flypie/SSEM-Baby/Docs/ctrlgate.pdf

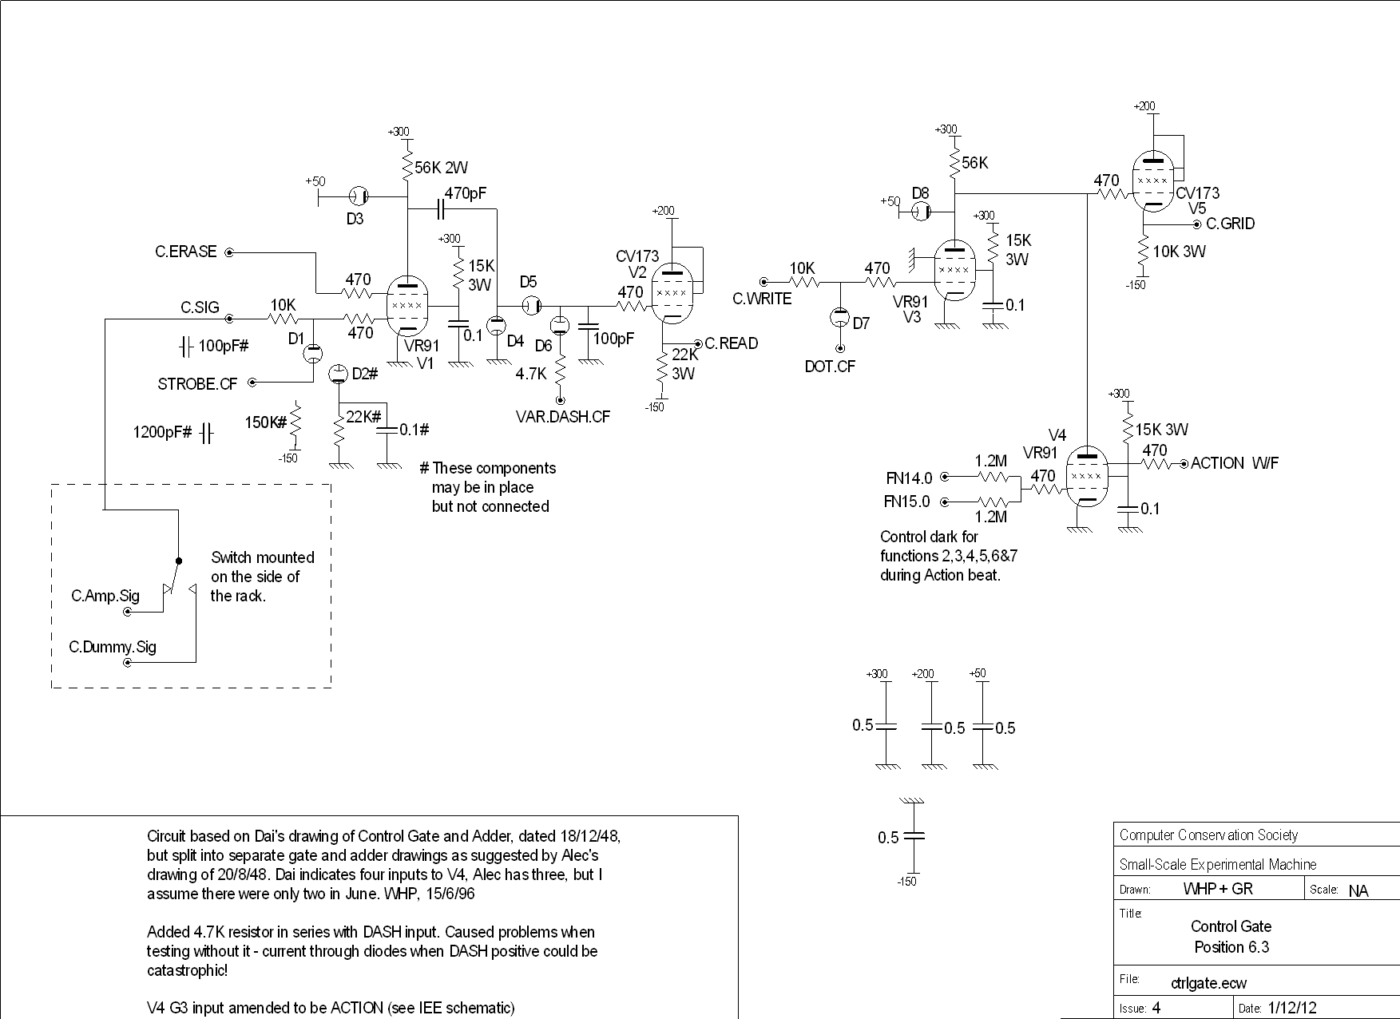
[picture p8: page 1]
