flypie/SSEM-Baby/Docs/transfer.pdf

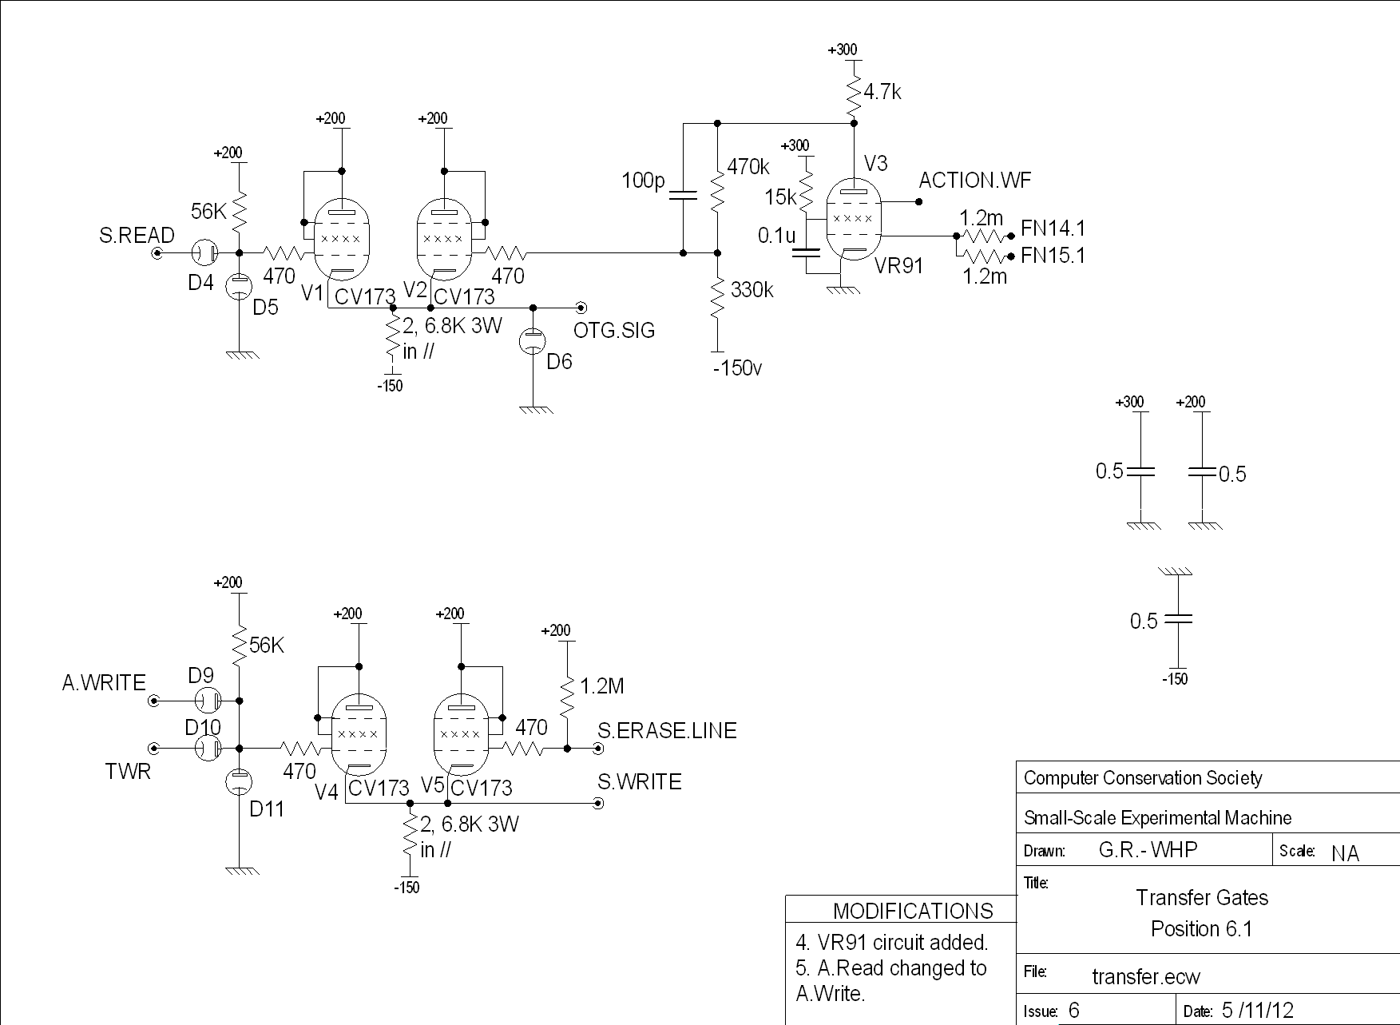
[picture p9: page 1]
