flypie/SSEM-Baby/Docs/crtamp3.pdf

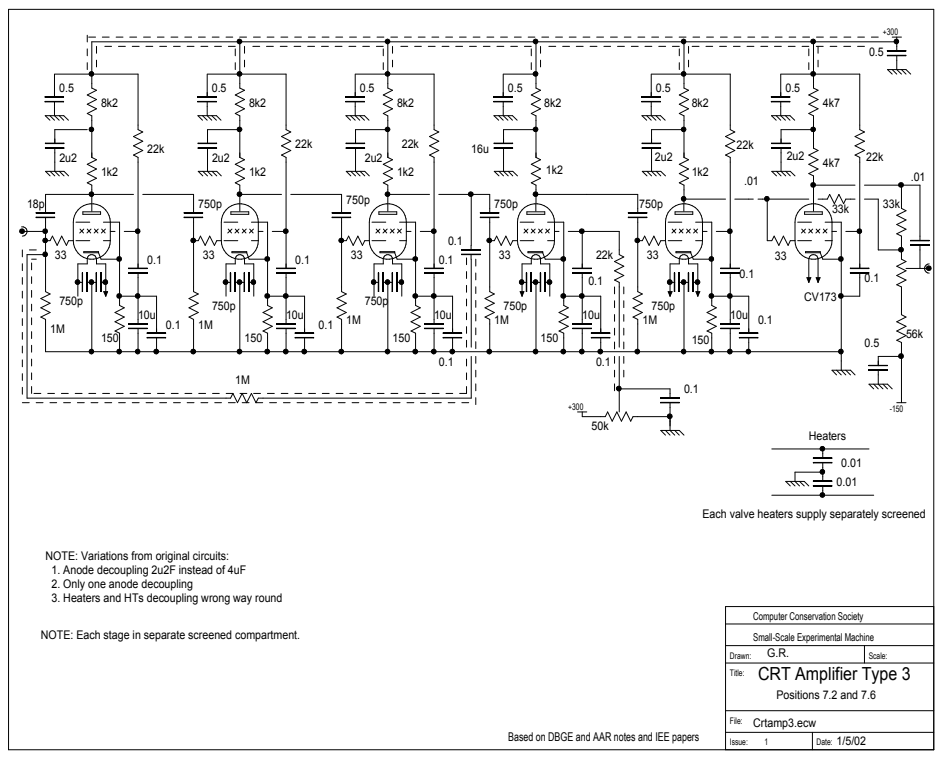
[picture p18: page 1]
Drawn:; Scale:; Title:; File:; Issue:; Date:; Heaters; Crtamp3.ecw; Positions 7.2 and 7.6

Each valve heaters supply separately screened

NOTE: Variations from original circuits:
1. Anode decoupling 2u2F instead of 4uF
2. Only one anode decoupling
3. Heaters and HTs decoupling wrong way round

Computer Conservation Society

NOTE: Each stage in separate screened compartment.

Small-Scale Experimental Machine
CRT Amplifier Type 3

1 Based on DBGE and AAR notes and IEE papers
