flypie/SSEM-Baby/Docs/crtamp4.pdf

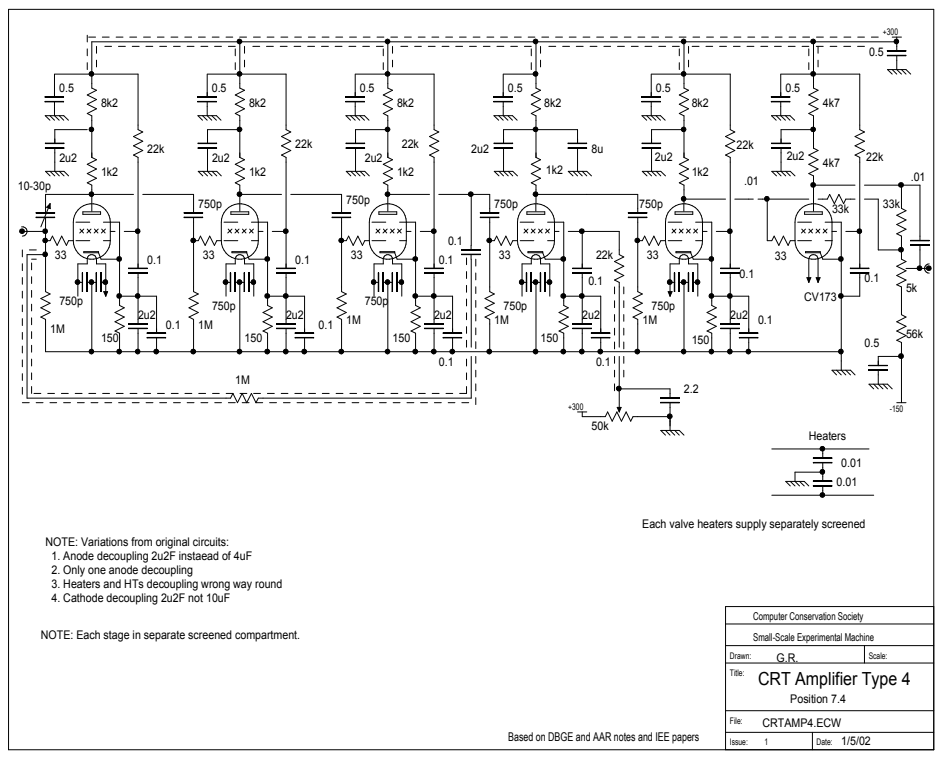
[picture p19: page 1]
Drawn:; Scale:; Title:; File:; Issue:; Date:; Heaters; Position 7.4; CRTAMP4.ECW

Each valve heaters supply separately screened

NOTE: Variations from original circuits:
1. Anode decoupling 2u2F instaead of 4uF
2. Only one anode decoupling
3. Heaters and HTs decoupling wrong way round
4. Cathode decoupling 2u2F not 10uF

Computer Conservation Society

NOTE: Each stage in separate screened compartment.

Small-Scale Experimental Machine
CRT Amplifier Type 4

1 Based on DBGE and AAR notes and IEE papers
