flypie/SSEM-Baby/Docs/crtcct3.pdf

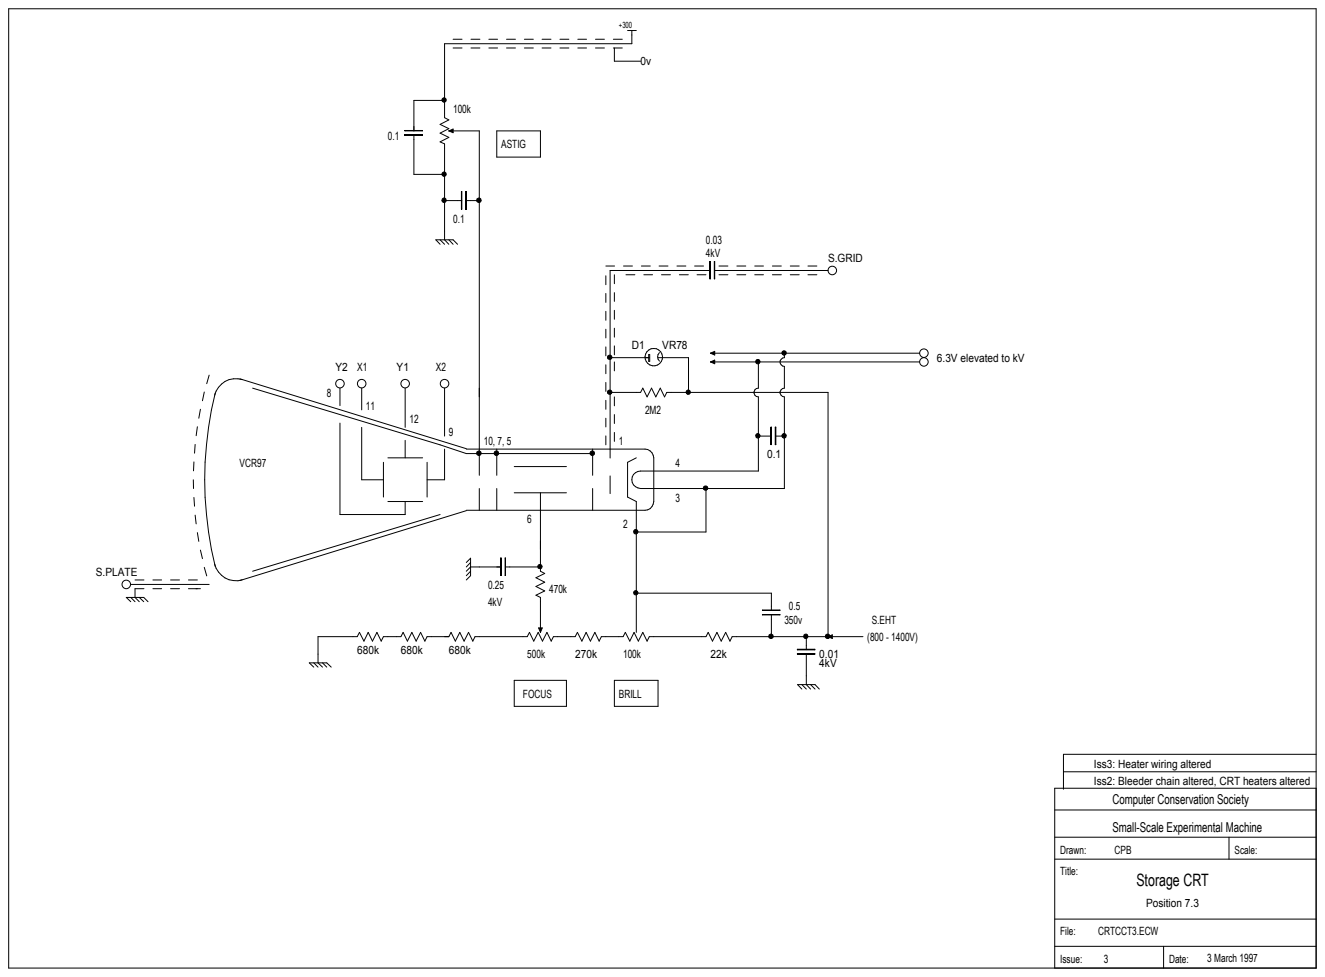
[picture p20: page 1]
Drawn:; Scale:; Title:; File:; Issue:; Date:; CPB; BRILL; FOCUS; VCR97; ASTIG; 3 March 1997; CRTCCT3.ECW; S.PLATE; S.GRID; Storage CRT; Position 7.3; S.EHT

6.3V elevated to kV

Iss3: Heater wiring altered
Iss2: Bleeder chain altered, CRT heaters altered
Computer Conservation Society

Small-Scale Experimental Machine
