flypie/SSEM-Baby/Docs/crtcct4.pdf

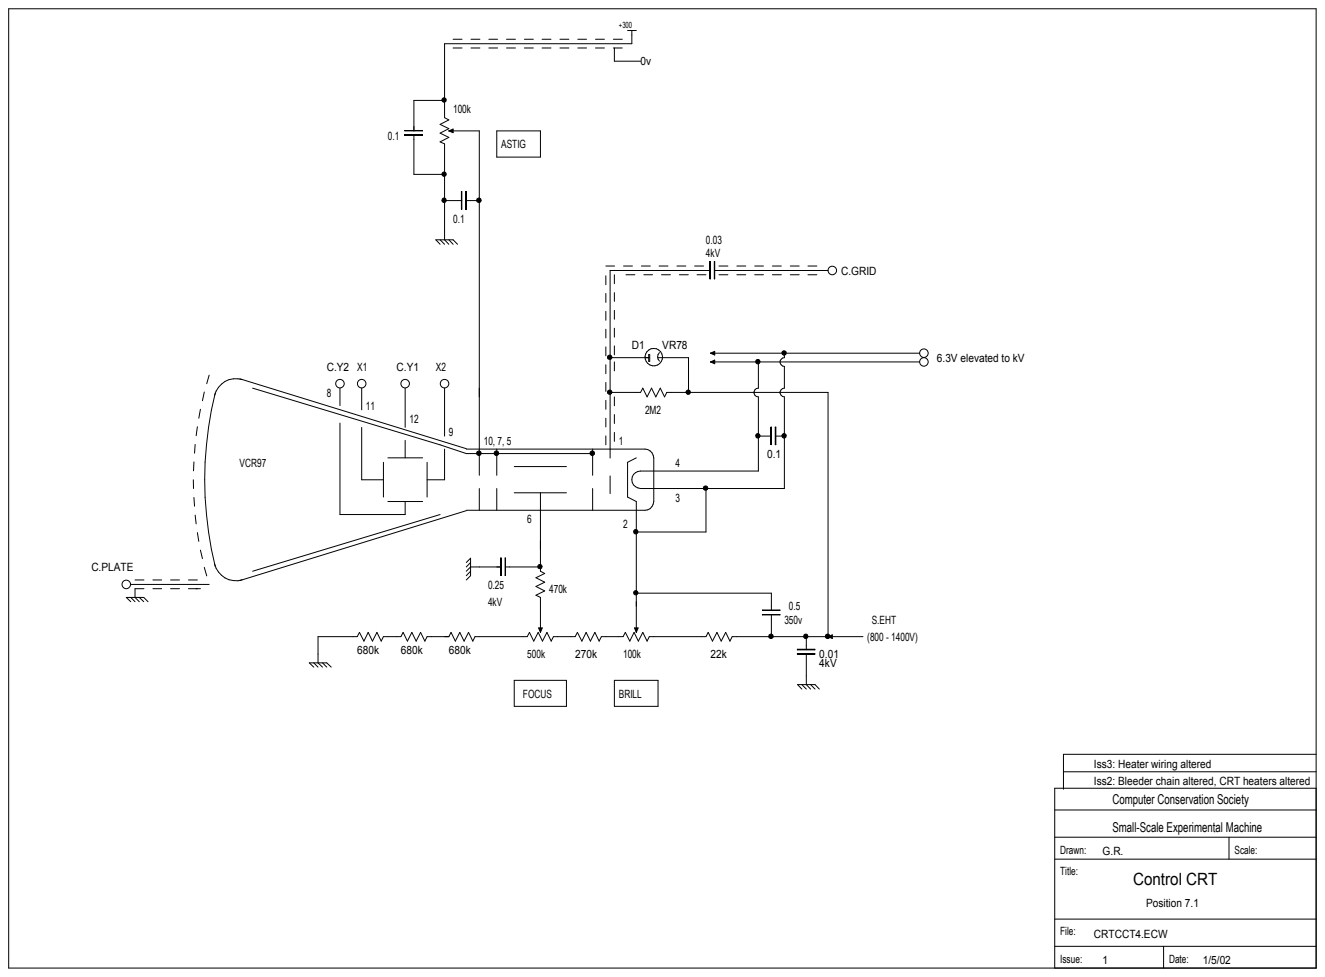
[picture p21: page 1]
Drawn:; Scale:; Title:; File:; Issue:; Date:; BRILL; FOCUS; VCR97; ASTIG; C.PLATE; C.GRID; Position 7.1; Control CRT; CRTCCT4.ECW; S.EHT

6.3V elevated to kV

Iss3: Heater wiring altered
Iss2: Bleeder chain altered, CRT heaters altered
Computer Conservation Society

Small-Scale Experimental Machine
