flypie/SSEM-Baby/Docs/crtcct5.pdf

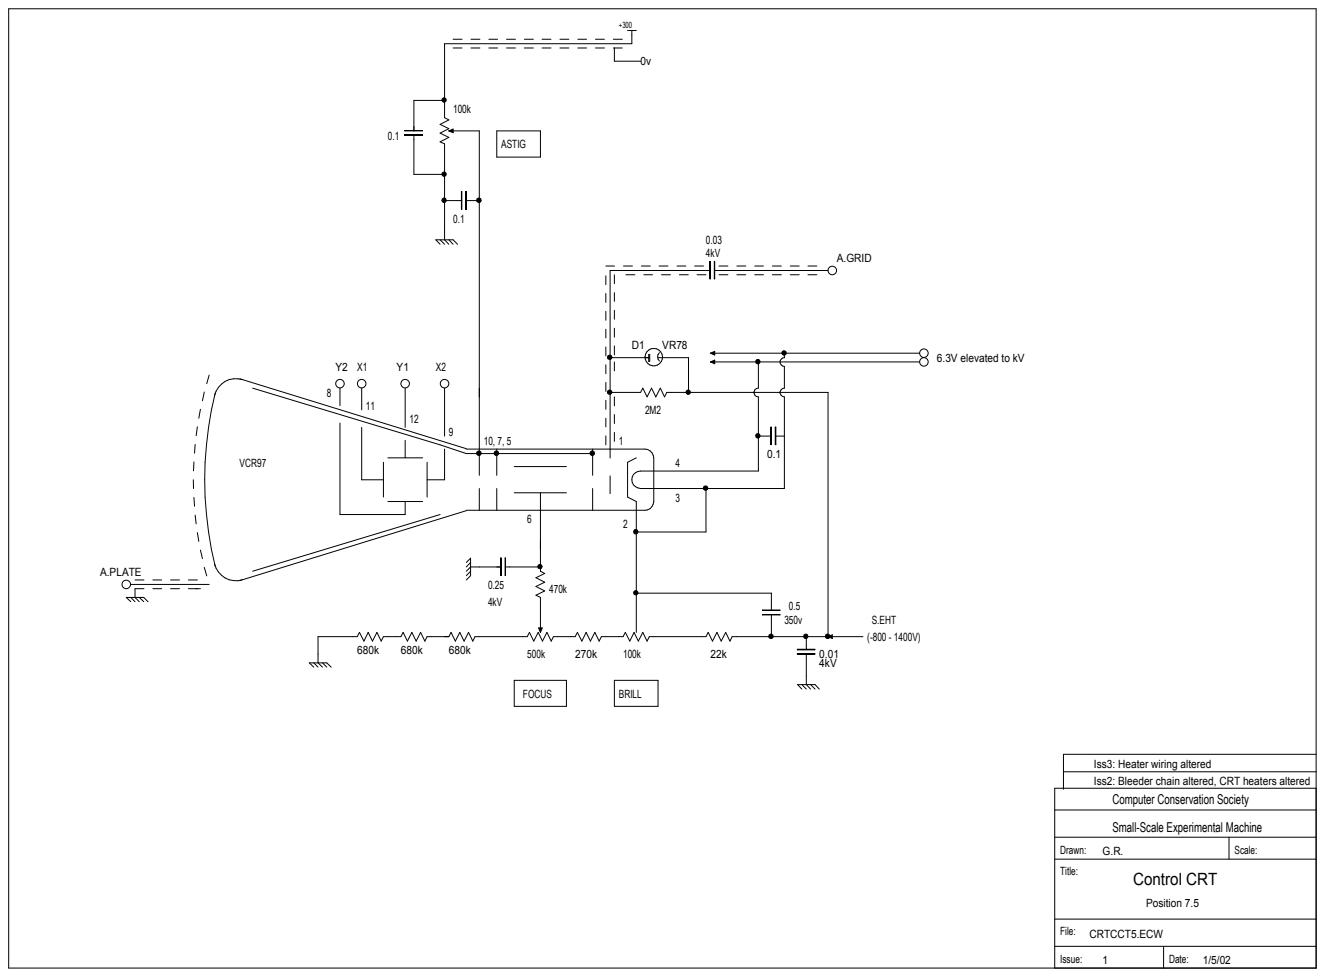
[picture p22: page 1]
Drawn:; Scale:; Title:; File:; Issue:; Date:; BRILL; FOCUS; VCR97; ASTIG; Control CRT; A.PLATE; A.GRID; Position 7.5; CRTCCT5.ECW; S.EHT

6.3V elevated to kV

Iss3: Heater wiring altered
Iss2: Bleeder chain altered, CRT heaters altered
Computer Conservation Society

Small-Scale Experimental Machine
