flypie/SSEM-Baby/Docs/crthtrtf.pdf

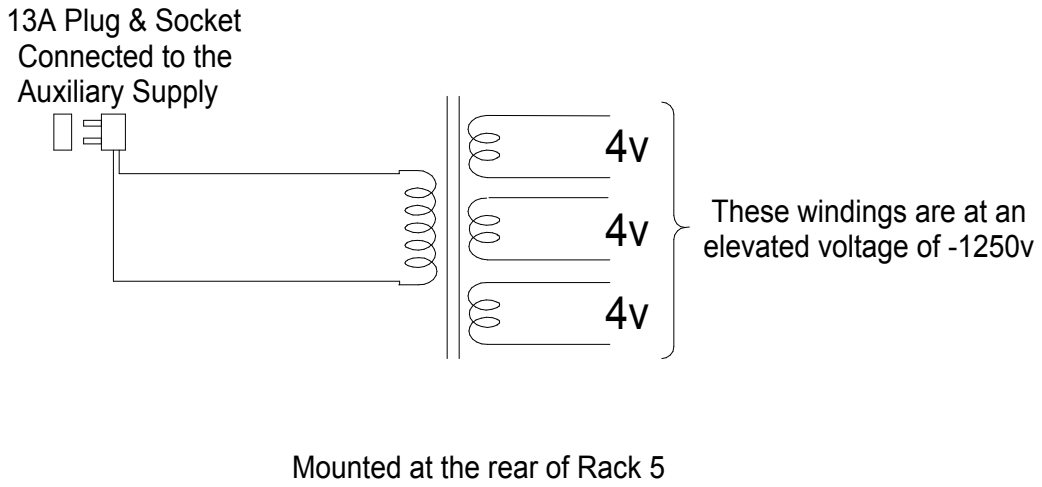
[picture p23: page 1]
Drawn:; Scale:; Title:; File:; Issue:; Date:; CRTHTRTF.ECW; Position 5.9

13A Plug & Socket
Connected to the
Auxiliary Supply

These windings are at an

elevated voltage of -1250v

Mounted at the rear of Rack 5

Computer Conservation Society

Small-Scale Experimental Machine

CRT Heater Transformer
