flypie/SSEM-Baby/Docs/crtpcif2.pdf

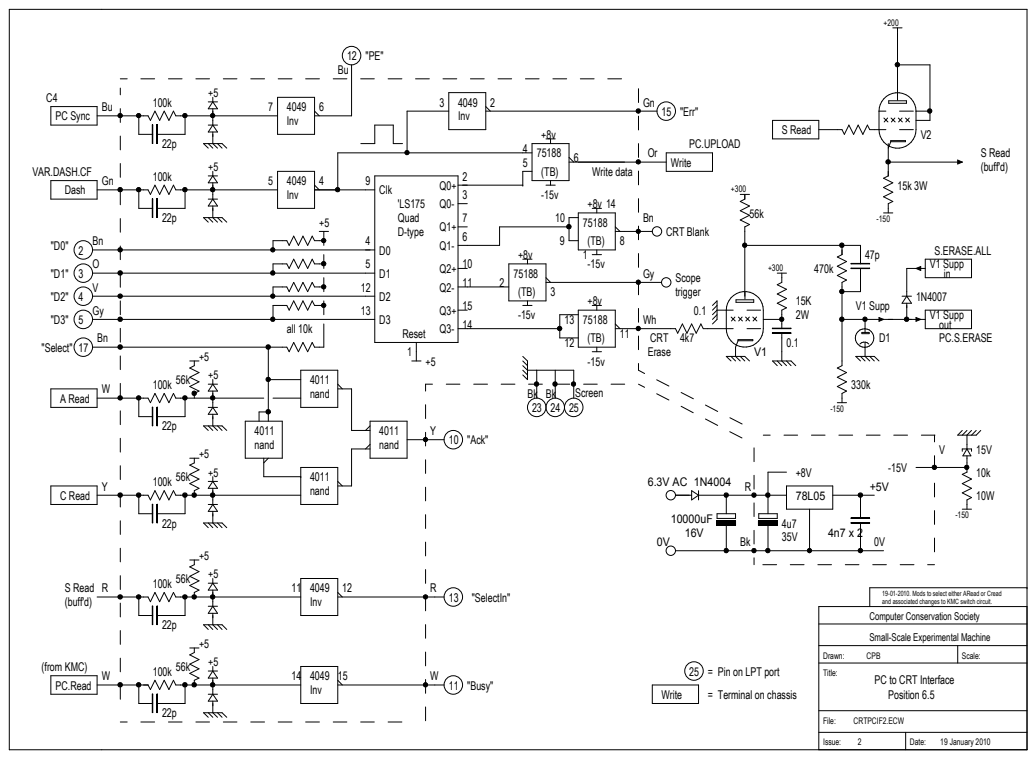
[picture p24: page 1]
Drawn:; Scale:; Title:; File:; Issue:; Date:; CPB; CRTPCIF2.ECW; 19 January 2010; S Read; S Read (buff'd); Clk; 'LS175 Quad D-type; Reset; 4049 Inv; CRT Blank; Scope trigger; Write; Write data; 15 "Err"; Inv; V1 Supp; out V1 Supp; V1 Supp in; CRT Erase; PC.UPLOAD; PC.S.ERASE; S.ERASE.ALL; Dash; PC Sync; VAR.DASH.CF; PC.Read; 11 "Busy"; Screen; C Read; 10 "Ack"; 4011 nand; A Read; (buff'd); "SelectIn"; "Select"; all 10k; (from KMC)

19-01-2010. Mods to select either ARead or Cread
and associated changes to KMC switch circuit.
Computer Conservation Society

Small-Scale Experimental Machine

= Pin on LPT port

PC to CRT Interface
Position 6.5

= Terminal on chassis
