flypie/SSEM-Baby/Docs/dchtrpu.pdf

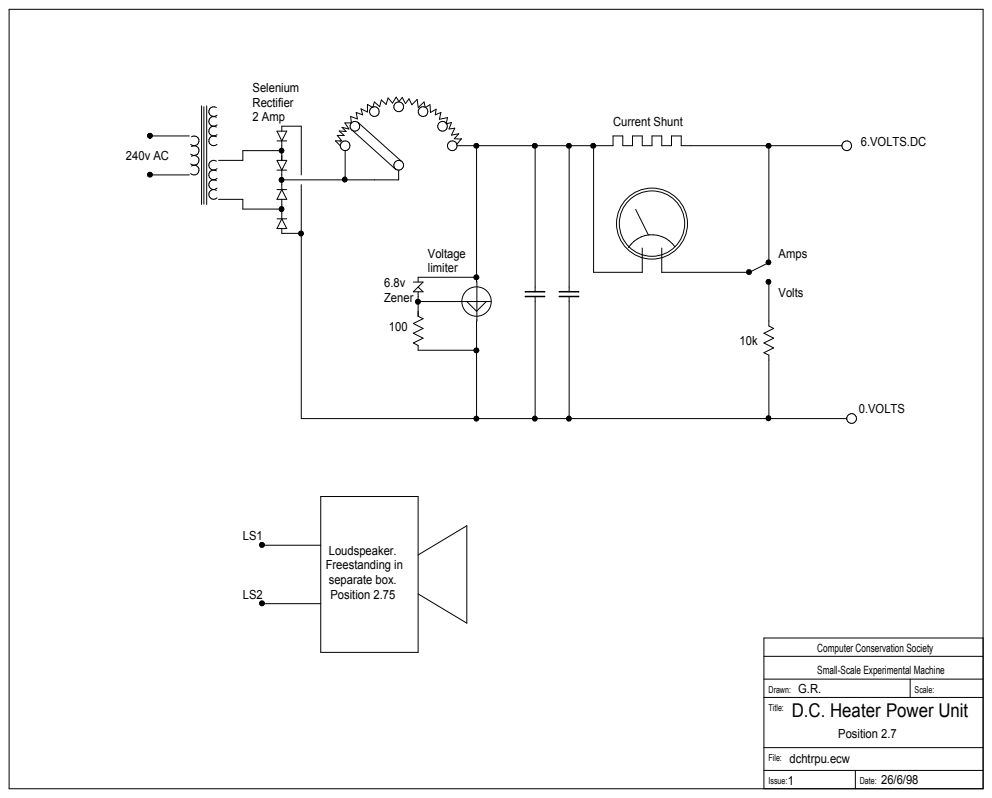
[picture p25: page 1]
Drawn:; Scale:; File:; Issue:; Date:; dchtrpu.ecw; Current Shunt; Selenium Rectifier 2 Amp; Voltage limiter; Amps; Volts; Position 2.7; 6.VOLTS.DC; 0.VOLTS; Loudspeaker. Freestanding in separate box. Position 2.75; 6.8v Zener

Computer Conservation Society

Small-Scale Experimental Machine
D.C. Heater Power Unit
Title:
