flypie/SSEM-Baby/Docs/keysw1.pdf

L 4 | L 3 | L 2 | L 1 | L 0

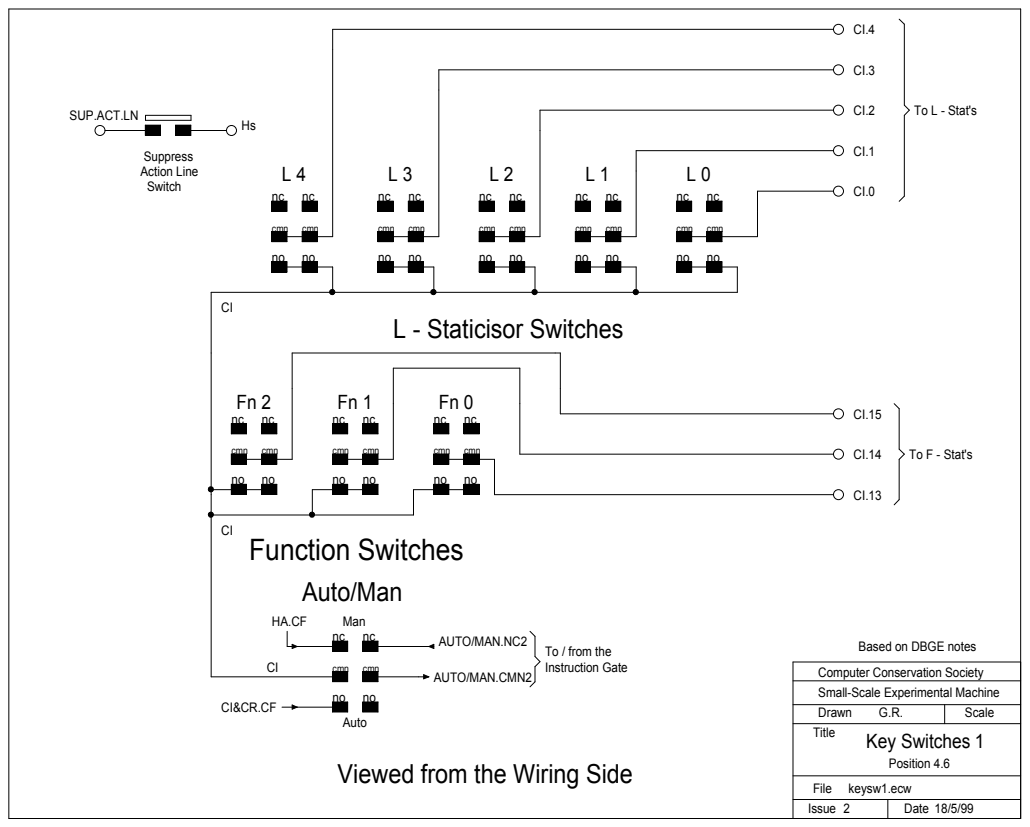
[picture p26: page 1]
Drawn; Scale; File; Issue; Date; keysw1.ecw; Auto/Man; Man; Auto; L - Staticisor Switches; Function Switches; AUTO/MAN.NC2; AUTO/MAN.CMN2; To L - Stat's; To F - Stat's; Position 4.6; Suppress Action Line Switch; cmn

SUP.ACT.LN

To / from the
Instruction Gate

Based on DBGE notes

Computer Conservation Society
Small-Scale Experimental Machine
Title
Key Switches 1

Viewed from the Wiring Side
