flypie/SSEM-Baby/Docs/keysw2.pdf

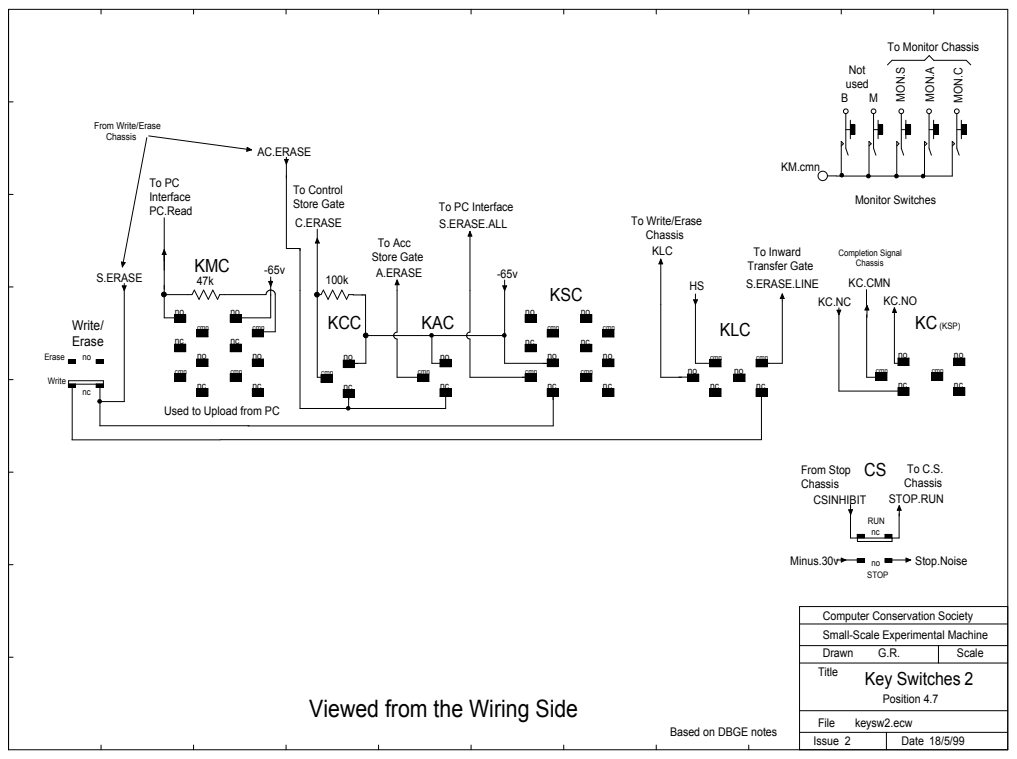
[picture p27: page 1]
Drawn; Scale; File; Issue; Date; keysw2.ecw; Write/ Erase; Write; Erase; S.ERASE; Position 4.7; From Stop Chassis; To C.S. Chassis; CSINHIBIT; STOP.RUN; RUN; Minus.30v; Stop.Noise; STOP; KCC; KAC; KSC; KLC; KC(KSP); C.ERASE; To Control Store Gate; A.ERASE; S.ERASE.ALL; To Acc Store Gate; S.ERASE.LINE; To Inward Transfer Gate; Completion Signal Chassis; KC.CMN; Monitor Switches; KM.cmn; Not used; MON.S; MON.A; MON.C; KMC; AC.ERASE; To PC Interface; PC.Read; cmn

To Monitor Chassis

From Write/Erase
Chassis

To Write/Erase
KLC

Used to Upload from PC

Computer Conservation Society
Small-Scale Experimental Machine
Title
Key Switches 2

Viewed from the Wiring Side

Based on DBGE notes
