flypie/SSEM-Baby/Docs/kvpsu1.pdf

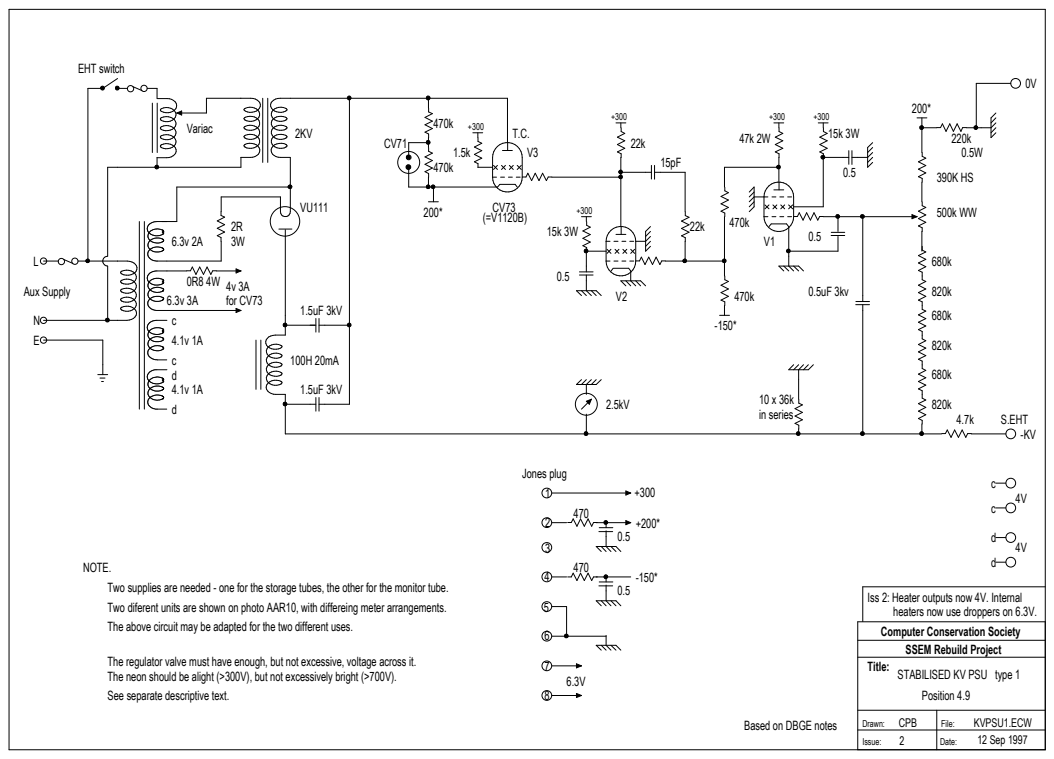
[picture p28: page 1]
Aux Supply; EHT switch; 2KV Variac; 10 x 36k in series; Jones plug; for CV73; S.EHT

NOTE.
Two supplies are needed - one for the storage tubes, the other for the monitor tube.
Two diferent units are shown on photo AAR10, with differeing meter arrangements.
The above circuit may be adapted for the two different uses.

Iss 2: Heater outputs now 4V. Internal
heaters now use droppers on 6.3V.
Computer Conservation Society
SSEM Rebuild Project

The regulator valve must have enough, but not excessive, voltage across it.
The neon should be alight (>300V), but not excessively bright (>700V).
See separate descriptive text.

Title:
STABILISED KV PSU type 1
Position 4.9

Based on DBGE notes

Drawn: CPB | KVPSU1.ECW File:

2 Issue: | 12 Sep 1997 Date:
