flypie/SSEM-Baby/Docs/kvpsu2.pdf

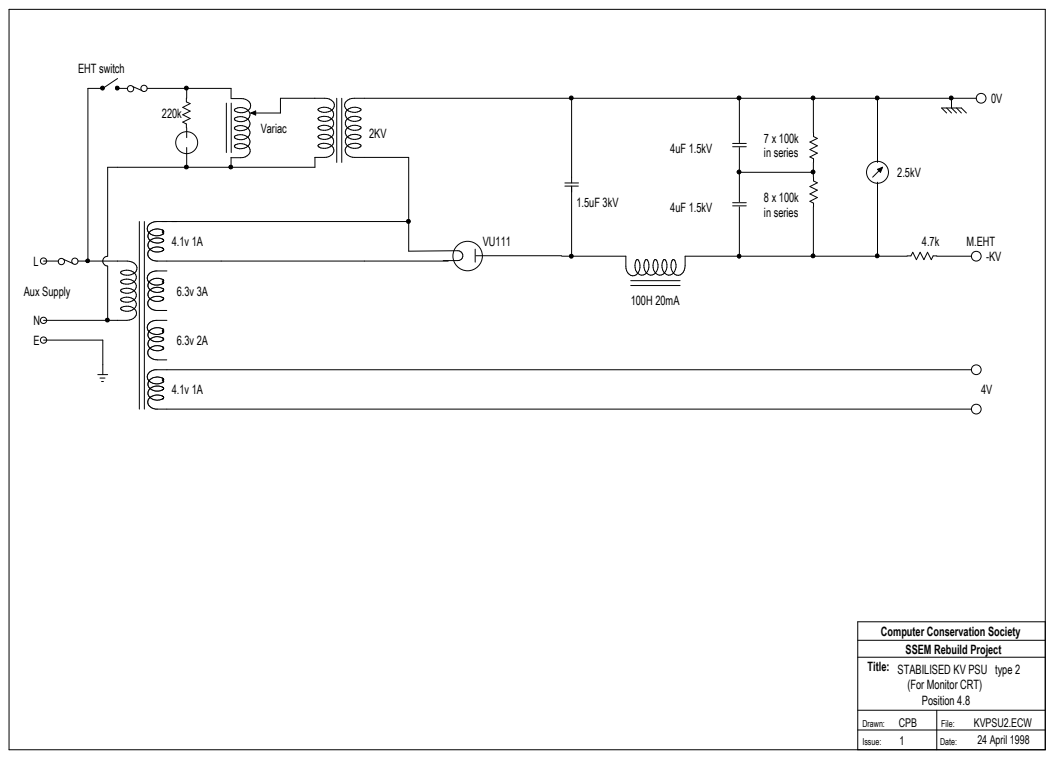
[picture p29: page 1]
Aux Supply; EHT switch; Title:; 2KV Variac; 7 x 100k in series; 8 x 100k in series; M.EHT

Computer Conservation Society
SSEM Rebuild Project
STABILISED KV PSU type 2
(For Monitor CRT)
Position 4.8

Drawn: CPB | KVPSU2.ECW File:

1 Issue: | 24 April 1998 Date:
