flypie/SSEM-Baby/Docs/monicct.pdf

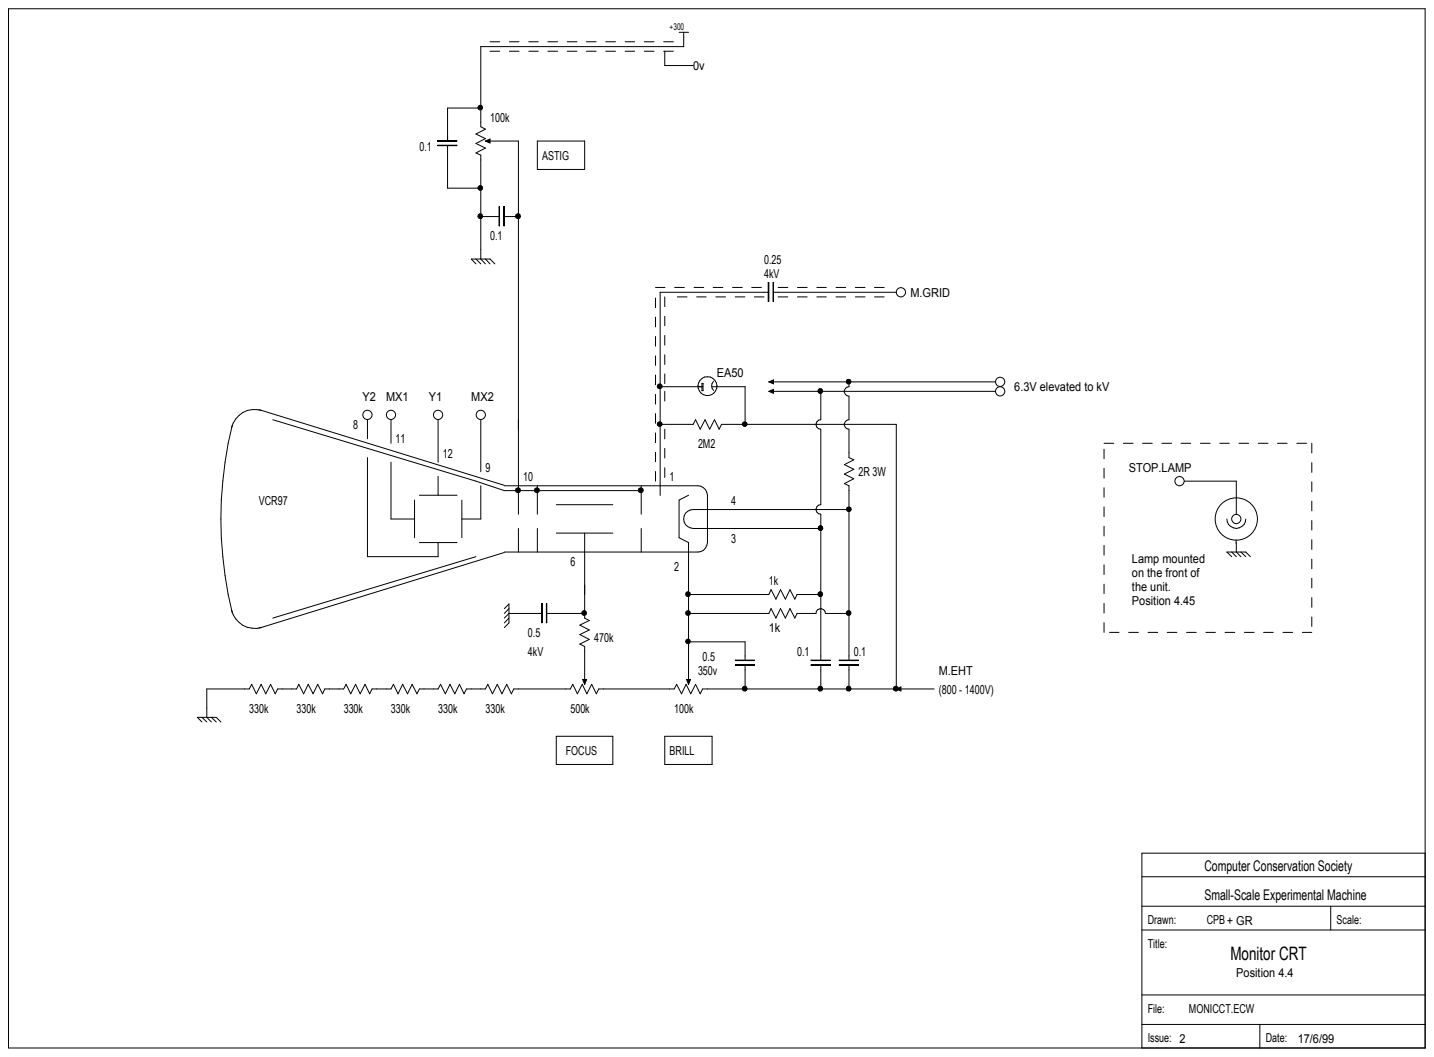
[picture p30: page 1]
Drawn:; Scale:; Title:; File:; Issue:; Date:; CPB; BRILL; FOCUS; VCR97; ASTIG; MONICCT.ECW; M.EHT; M.GRID; Monitor CRT; Position 4.4; STOP.LAMP

6.3V elevated to kV

Lamp mounted
on the front of
the unit.
Position 4.45

Computer Conservation Society

Small-Scale Experimental Machine
