flypie/SSEM-Baby/Docs/powrctl6b.pdf

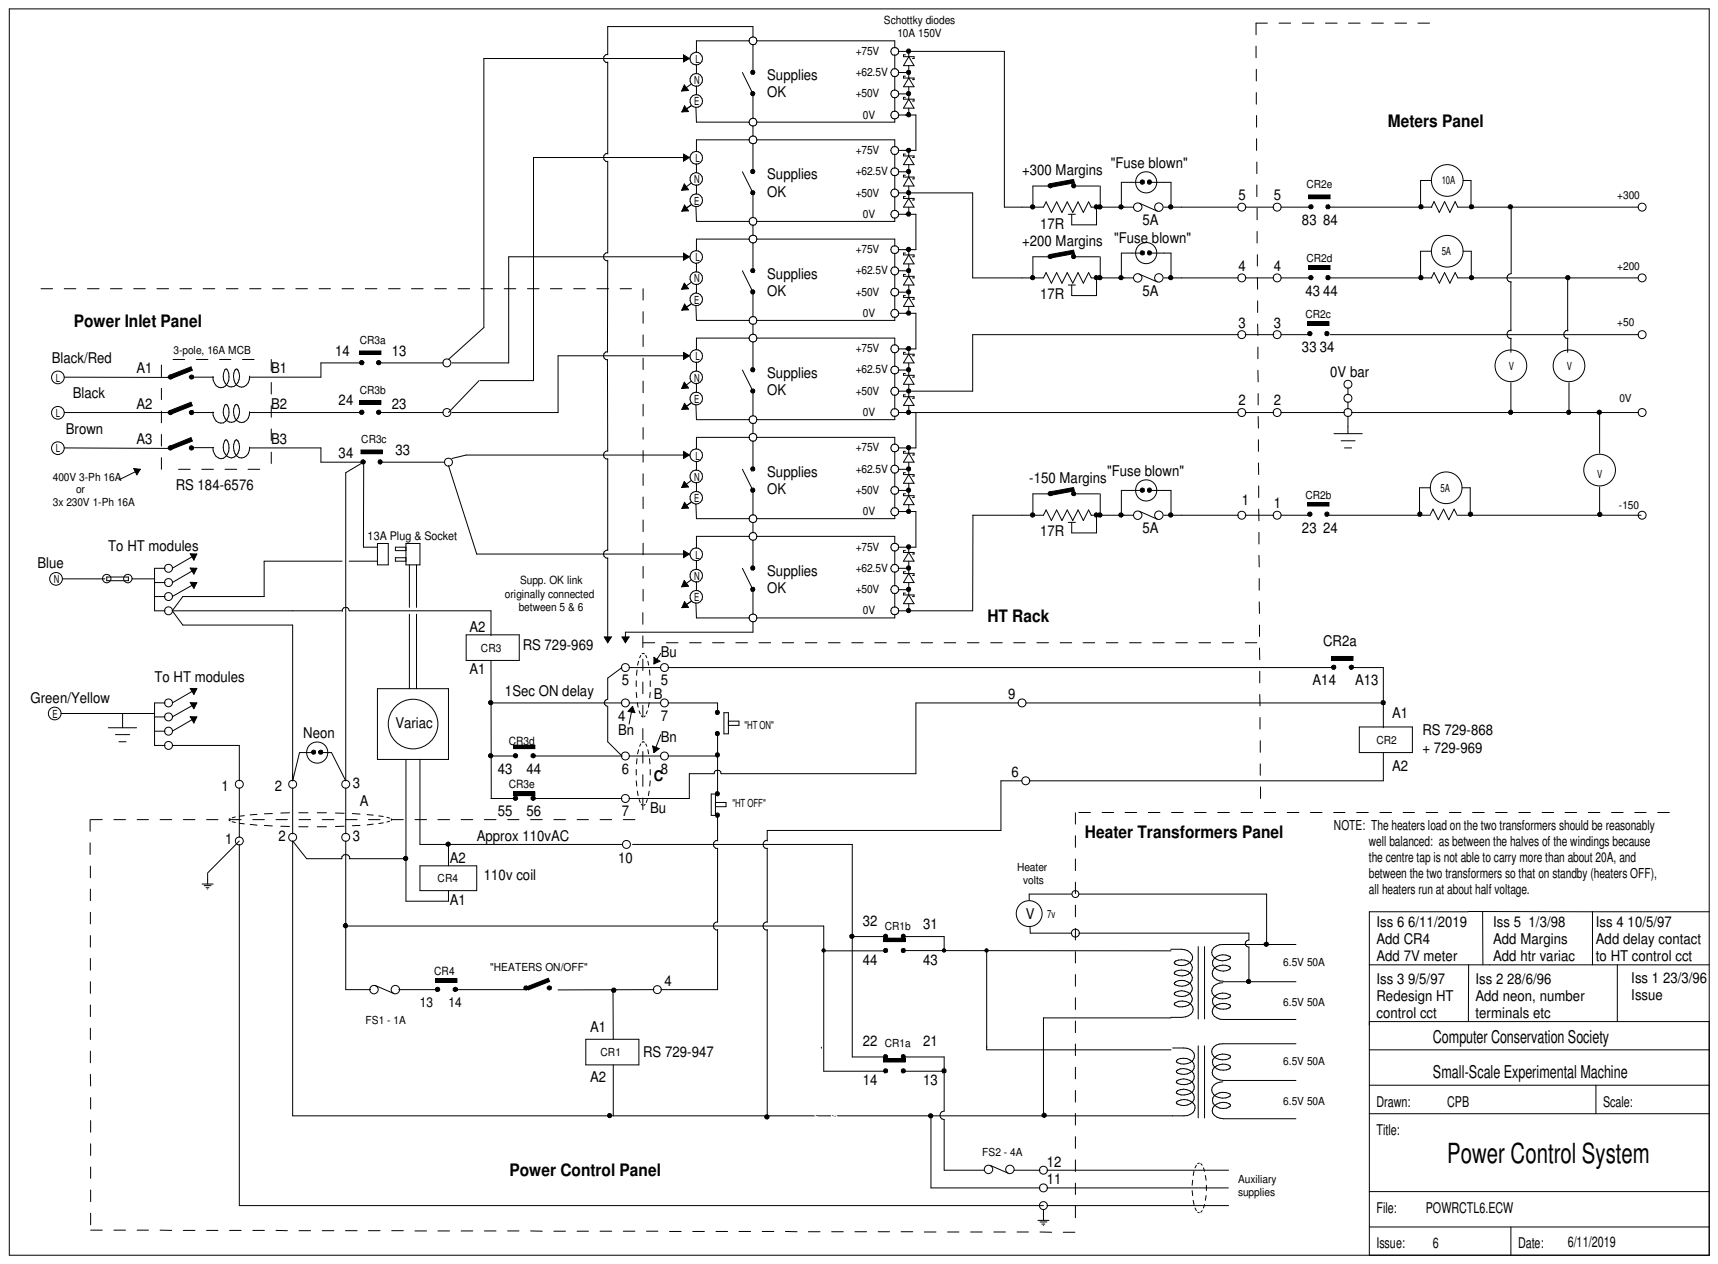
[picture p31: page 1]
Drawn:; Scale:; Title:; File:; Issue:; Date:; CPB; HT Rack; "HT OFF"; 1Sec ON delay; 13A Plug & Socket; Blue; Supplies OK; Green/Yellow; 3-pole, 16A MCB; Black/Red; Black; Brown; Schottky diodes 10A 150V; CR3d Neon; Auxiliary supplies; Heater volts; Variac; V 0V bar; "Fuse blown"; +300 Margins; +200 Margins; 110v coil; Approx 110vAC; POWRCTL6.ECW; Meters Panel

Power Inlet Panel

"Fuse blown" -150 Margins

To HT modules

Supp. OK link
originally connected
between 5 & 6

Heater Transformers Panel

NOTE: The heaters load on the two transformers should be reasonably
well balanced: as between the halves of the windings because
the centre tap is not able to carry more than about 20A, and
between the two transformers so that on standby (heaters OFF),
all heaters run at about half voltage.

Iss 6 6/11/2019 Add CR4 Add 7V meter | Iss 5 1/3/98 Add Margins Add htr variac | Iss 4 10/5/97 Add delay contact to HT control cct

"HEATERS ON/OFF"

Iss 3 9/5/97 Redesign HT control cct | Iss 2 28/6/96 Add neon, number terminals etc | Iss 1 23/3/96 Issue

Computer Conservation Society

Small-Scale Experimental Machine

Power Control System

Power Control Panel
