flypie/SSEM-Baby/Docs/prepulse.pdf

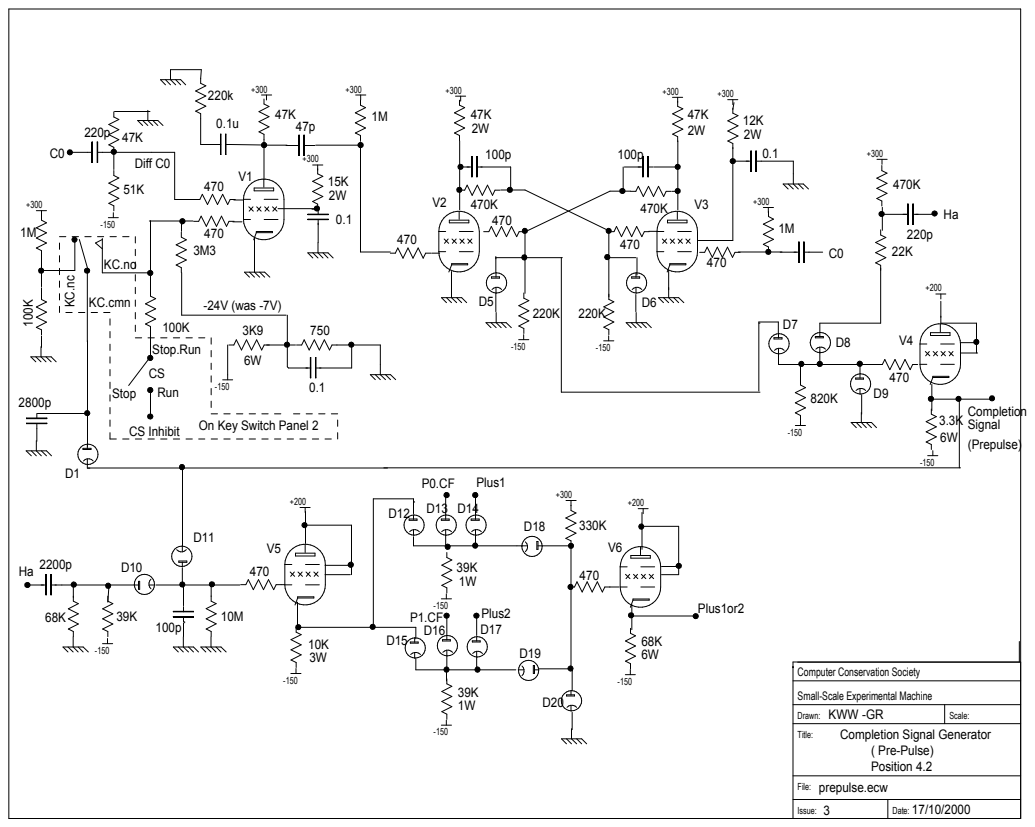
[picture p32: page 1]

On Key Switch Panel 2

Small-Scale Experimental Machine
KWW
Completion Signal Generator
( Pre-Pulse)
Position 4.2
