flypie/SSEM-Baby/Docs/rmondrs.pdf

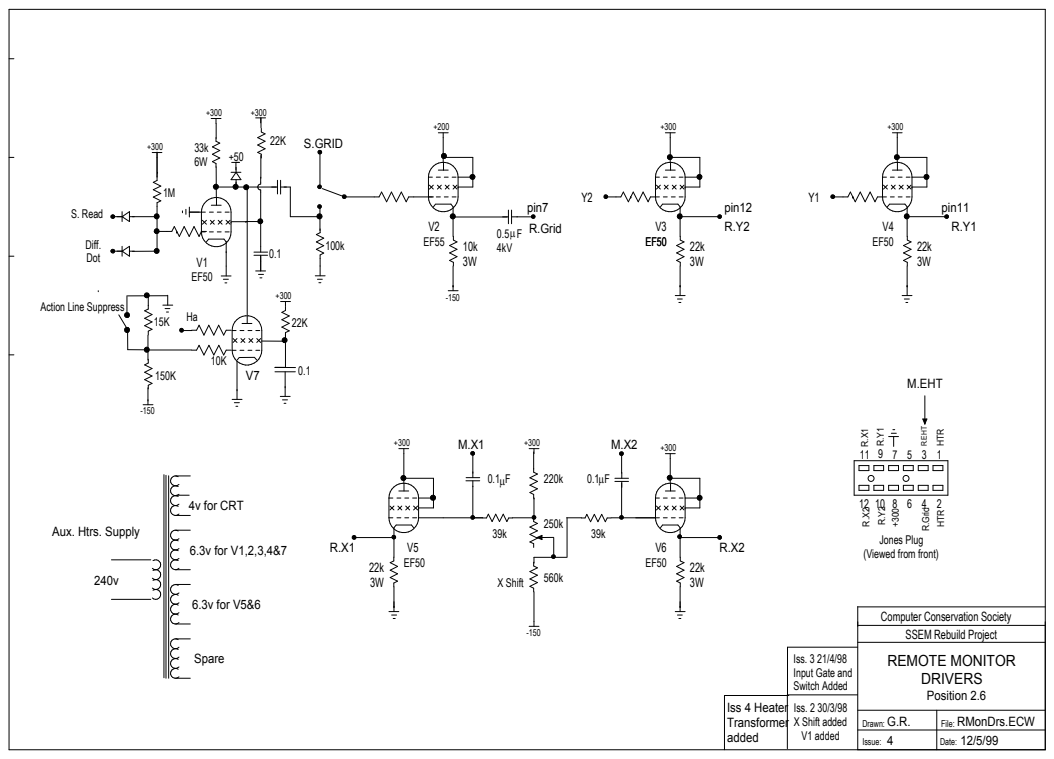
[picture p33: page 1]
S. Read; Diff. Dot; X Shift; pin7; pin12; pin11; R.Grid; HTR HTR; S.GRID; 4v for CRT; 6.3v for V1,2,3,4&7; 6.3v for V5&6; Spare; M.EHT; R.EHT

Action Line Suppress

Aux. Htrs. Supply

Jones Plug
(Viewed from front)

Computer Conservation Society
SSEM Rebuild Project
REMOTE MONITOR
DRIVERS
Position 2.6

Iss. 3 21/4/98
Input Gate and
Switch Added

Iss 4 Heater Transformer added | Iss. 2 30/3/98 X Shift added V1 added

G.R. Drawn: | RMonDrs.ECW File:

4 Issue: | 12/5/99 Date:
