flypie/SSEM-Baby/Docs/scfollws.pdf

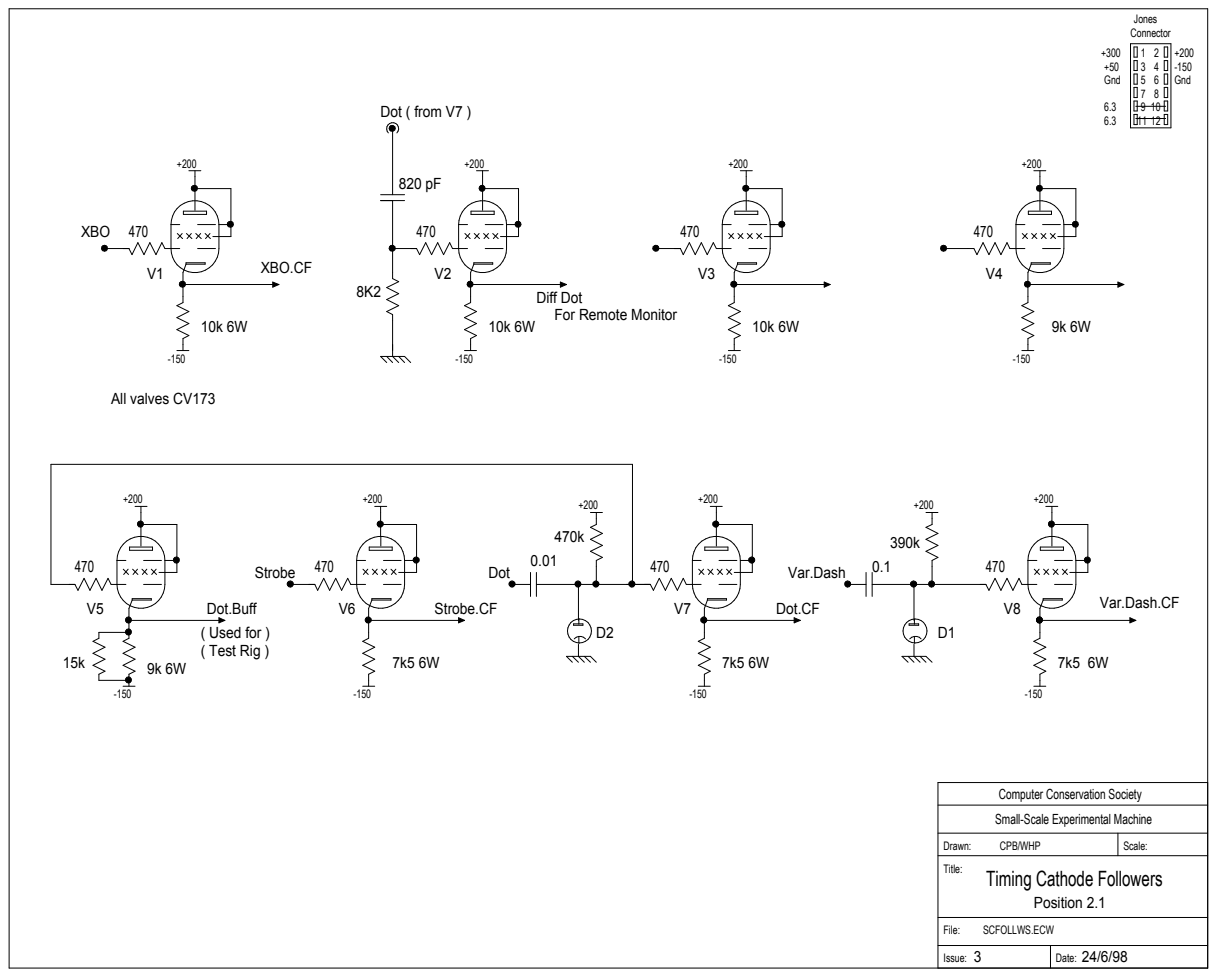
[picture p34: page 1]
Jones Connector; Gnd; Drawn:; Scale:; Title:; File:; Issue:; Date:; SCFOLLWS.ECW; CPB/WHP; Diff Dot; All valves CV173; Strobe; Dot; Dot.Buff; Strobe.CF; Dot.CF; Dot ( from V7 ); XBO; XBO.CF; ( Used for ) ( Test Rig ); Var.Dash; Position 2.1

For Remote Monitor

Var.Dash.CF V8

Computer Conservation Society
Small-Scale Experimental Machine

Timing Cathode Followers
