flypie/SSEM-Baby/Docs/sdot&stb.pdf

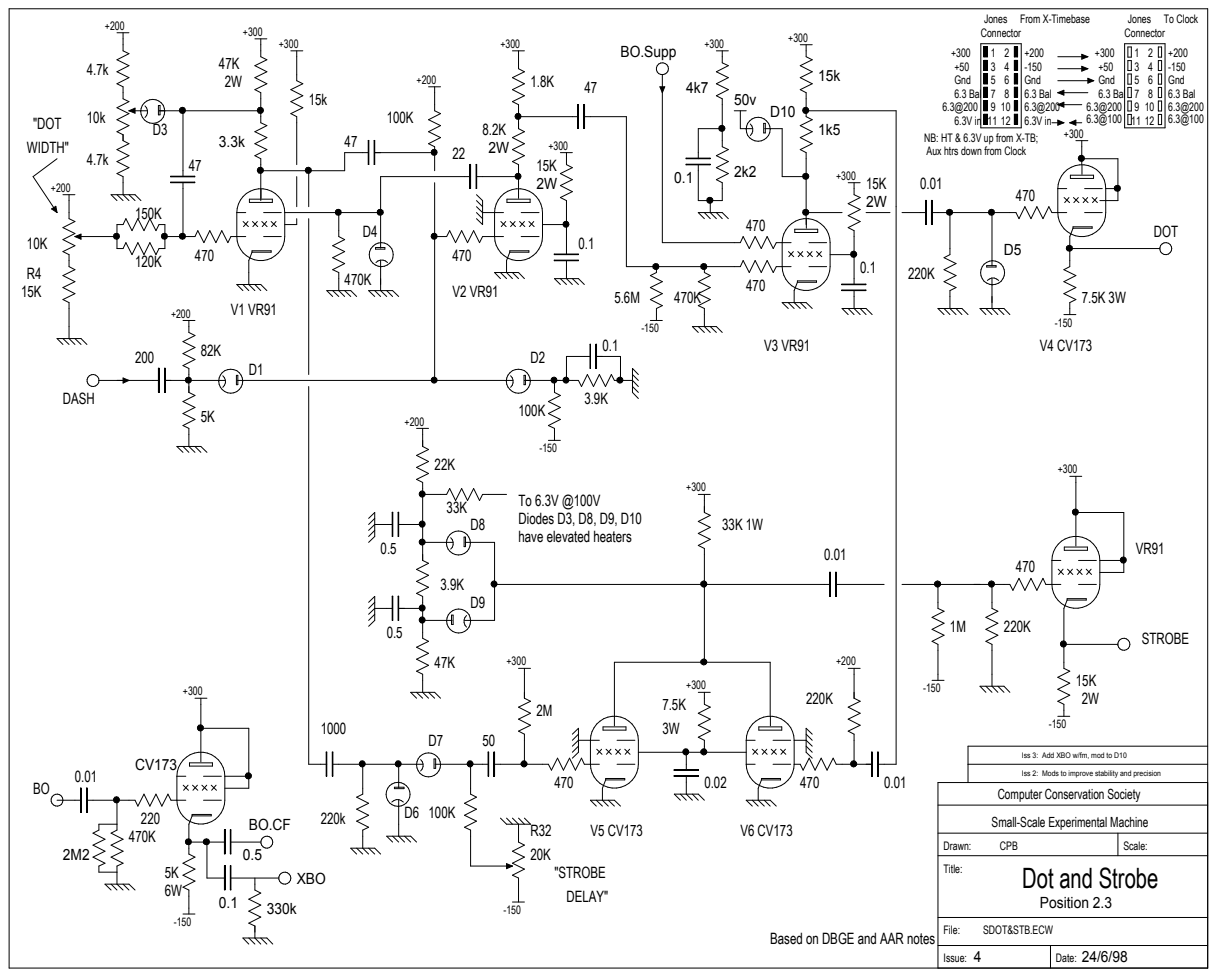
[picture p35: page 1]

NB: HT & 6.3V up from X-TB;
Aux htrs down from Clock

Iss 3: Add XBO w/fm, mod to D10

Iss 2: Mods to improve stability and precision
Computer Conservation Society

Small-Scale Experimental Machine

Based on DBGE and AAR notes
