flypie/SSEM-Baby/Docs/smonxtb.pdf

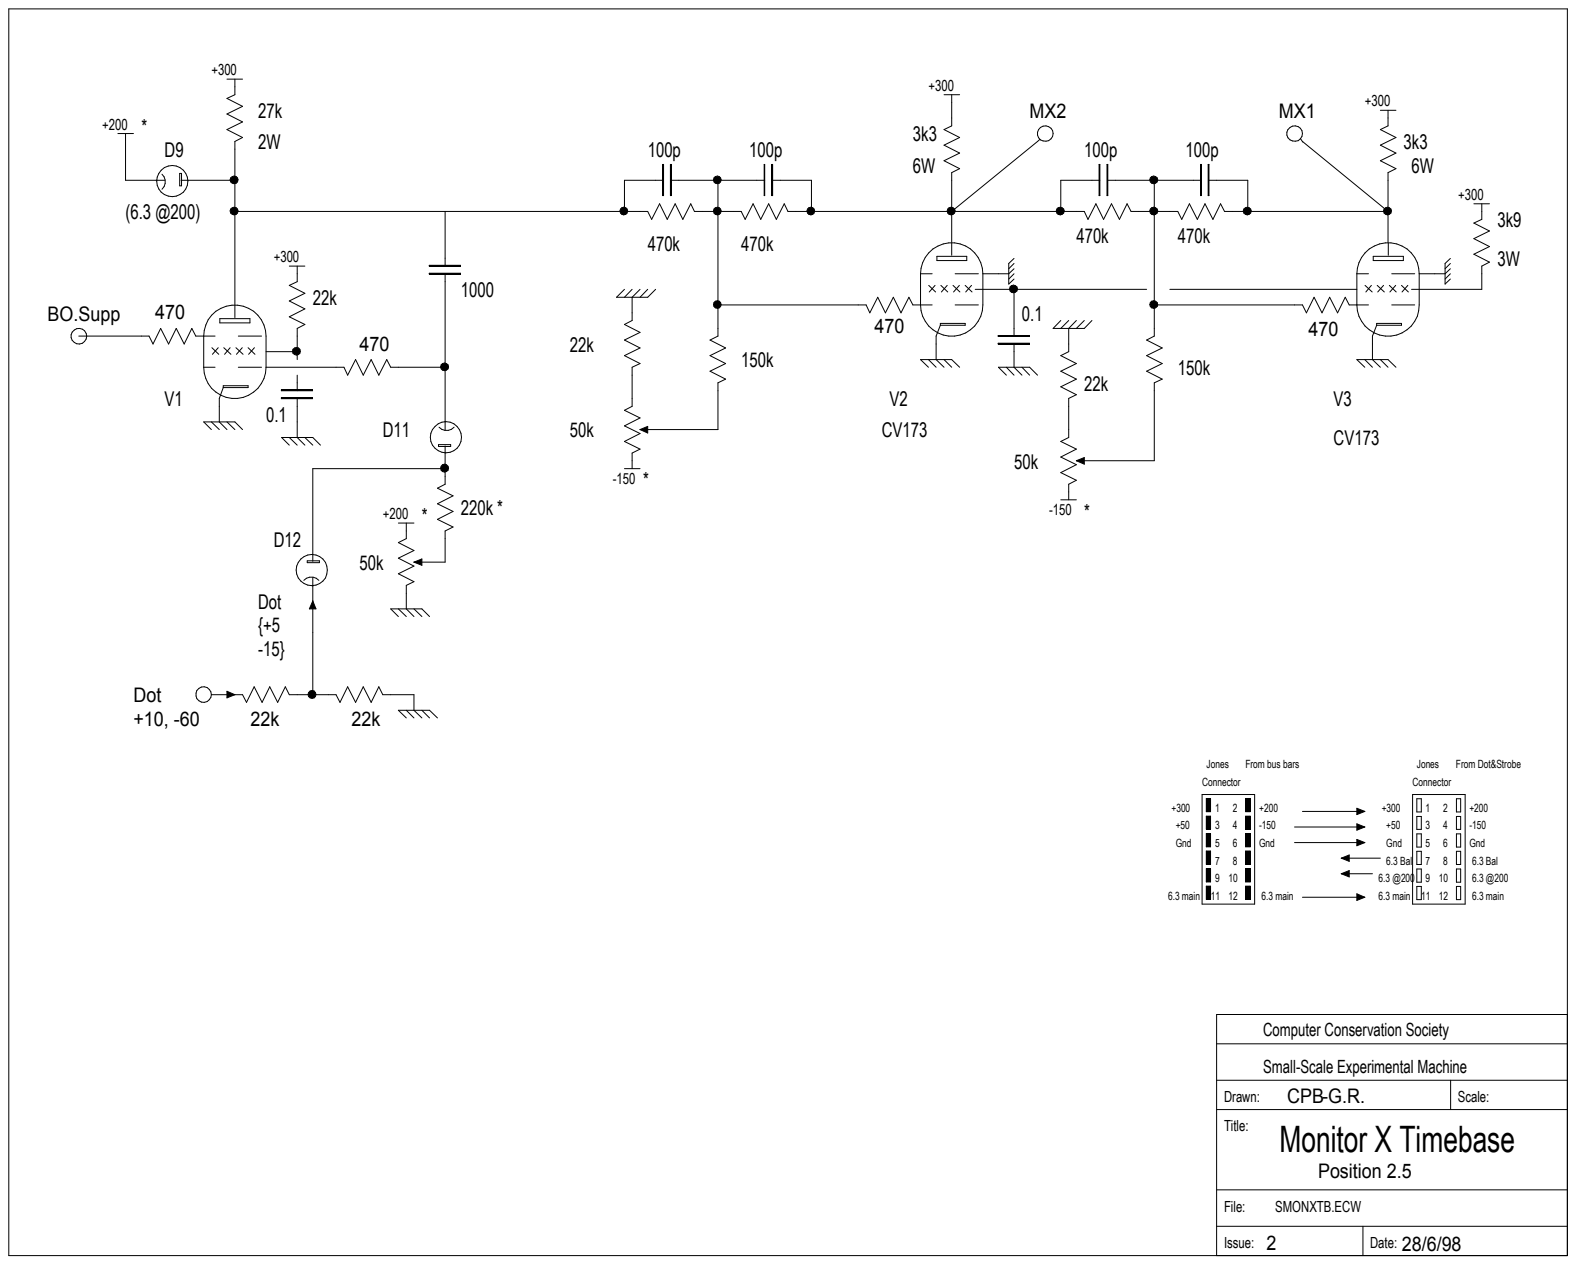
[picture p36: page 1]
Drawn:; Scale:; Title:; File:; Issue:; Date:; Jones; Connector; Gnd; From bus bars; From Dot&Strobe; 6.3 Bal; 6.3 main; SMONXTB.ECW; Dot {+5; BO.Supp; Dot +10, -60; Position 2.5

Computer Conservation Society

Small-Scale Experimental Machine
CPB-G.R.
Monitor X Timebase
