flypie/SSEM-Baby/Docs/stab200.pdf

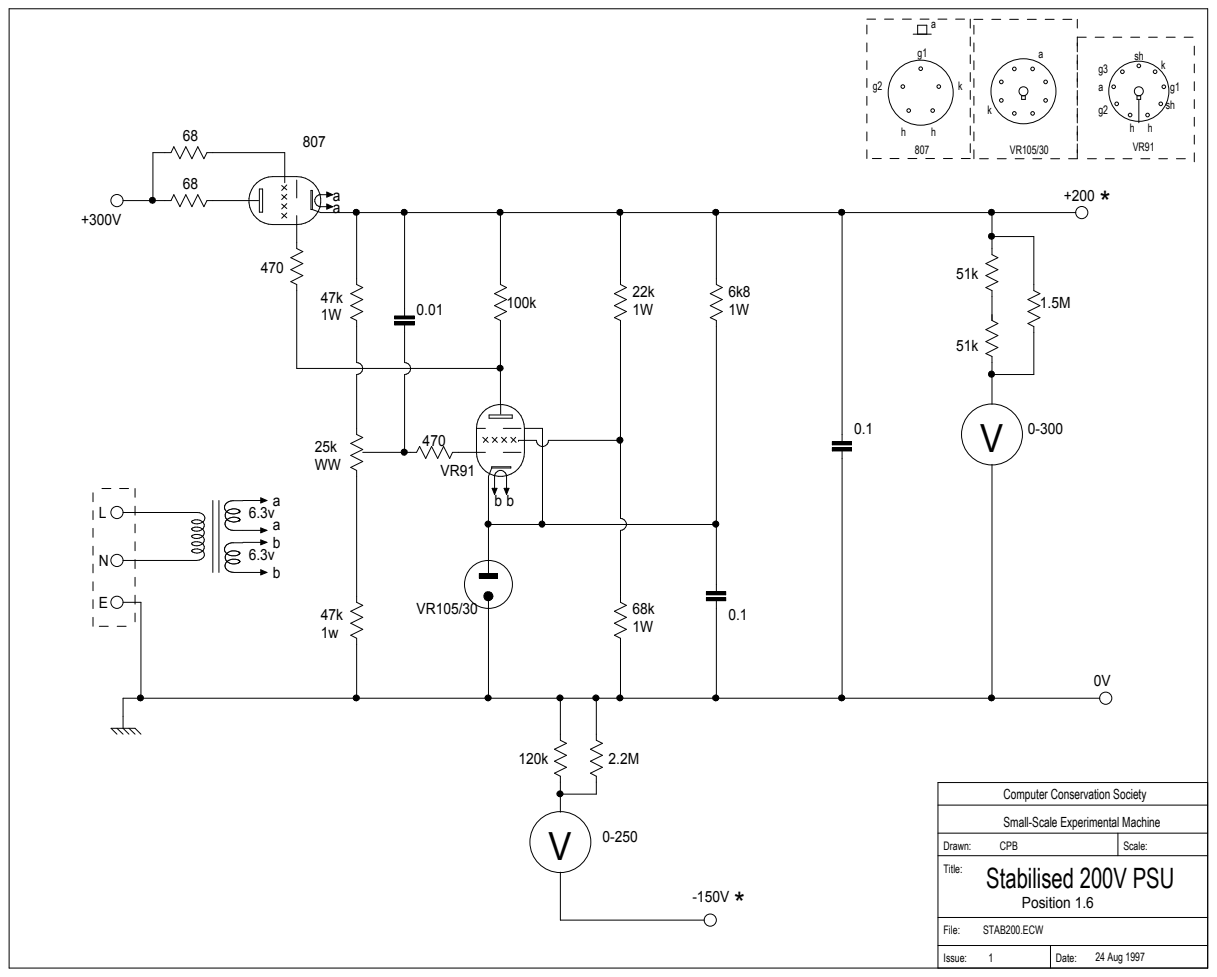
[picture p37: page 1]
Drawn:; Scale:; Title:; File:; Issue:; Date:; CPB; STAB200.ECW; 24 Aug 1997; Stabilised 200V PSU; Position 1.6

Computer Conservation Society

Small-Scale Experimental Machine
