flypie/SSEM-Baby/Docs/sxtmbase.pdf

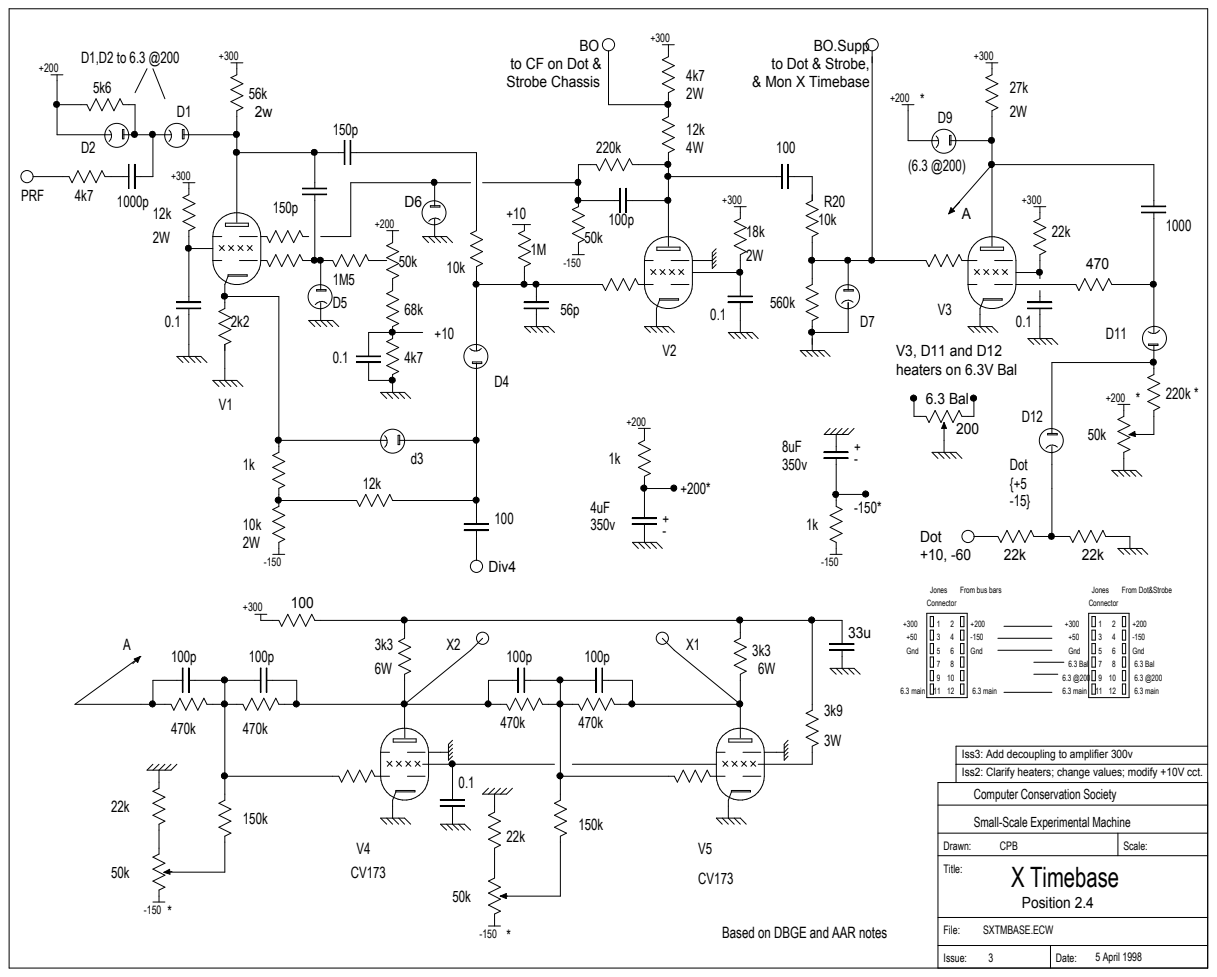
[picture p39: page 1]

to CF on Dot &
Strobe Chassis

Iss3: Add decoupling to amplifier 300v
Iss2: Clarify heaters; change values; modify +10V cct.
Computer Conservation Society

Small-Scale Experimental Machine
X Timebase
