flypie/SSEM-Baby/Docs/typewr.pdf

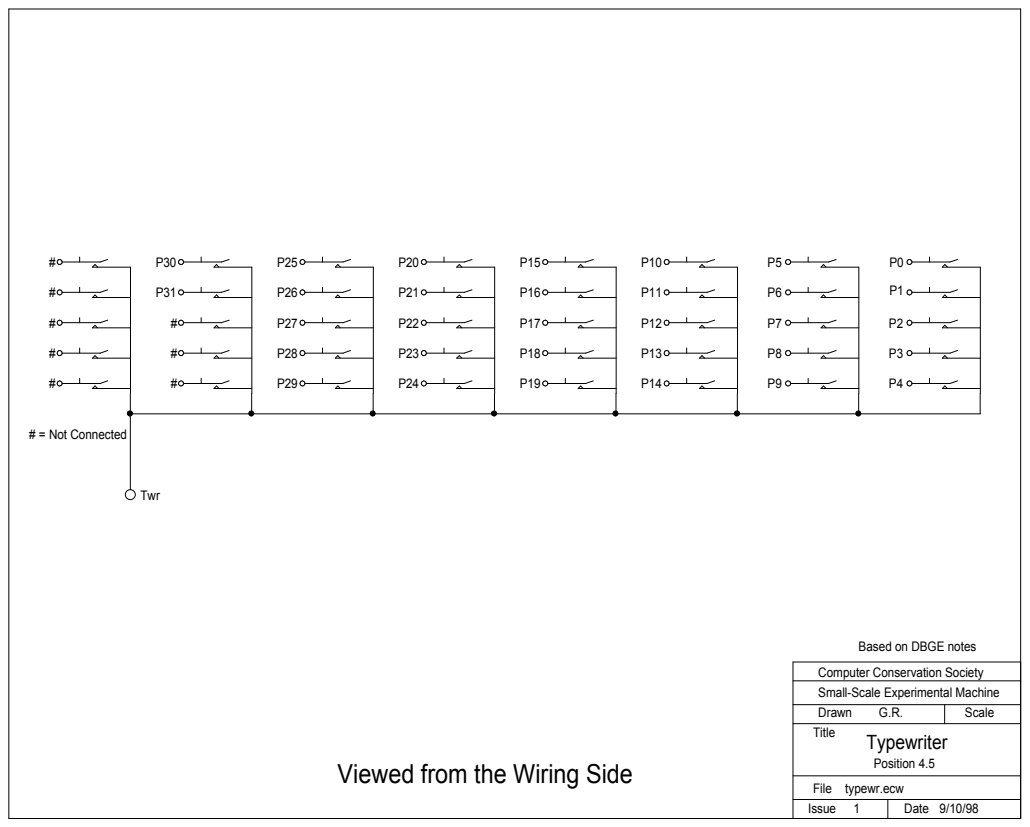
[picture p40: page 1]

Based on DBGE notes

Computer Conservation Society
Small-Scale Experimental Machine
Title
Typewriter

Viewed from the Wiring Side
