flypie/SSEM-Baby/Docs/cmoscrt3.pdf

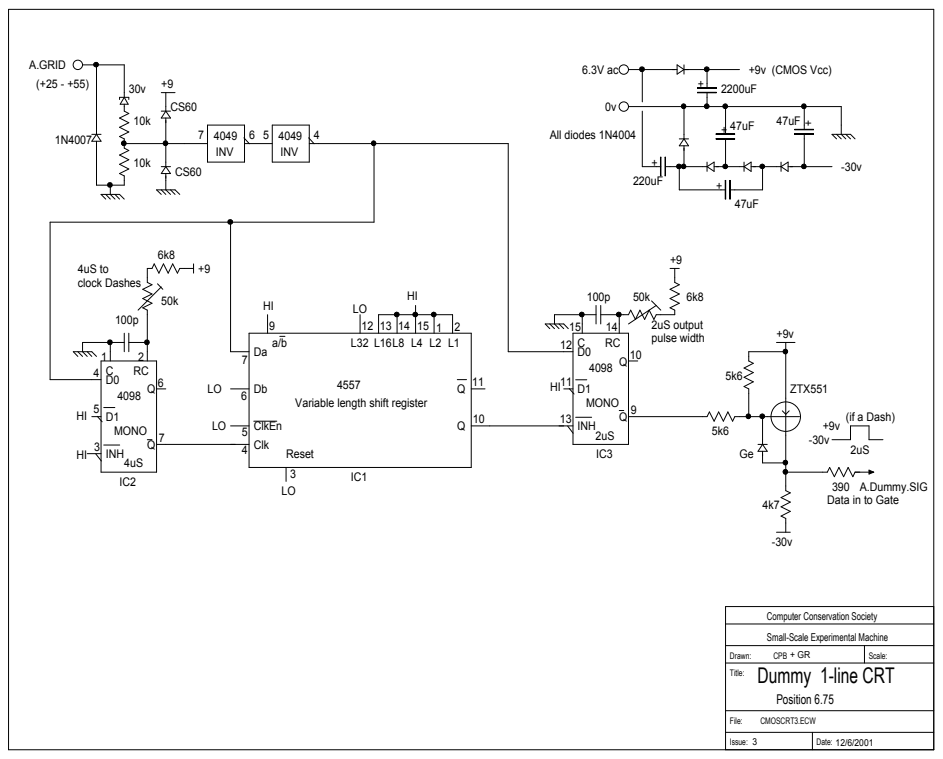
[picture p43: page 1]

Variable length shift register

A.Dummy.SIG
Data in to Gate

Small-Scale Experimental Machine
Dummy 1-line CRT
