flypie/SSEM-Baby/Docs/fstat13.pdf

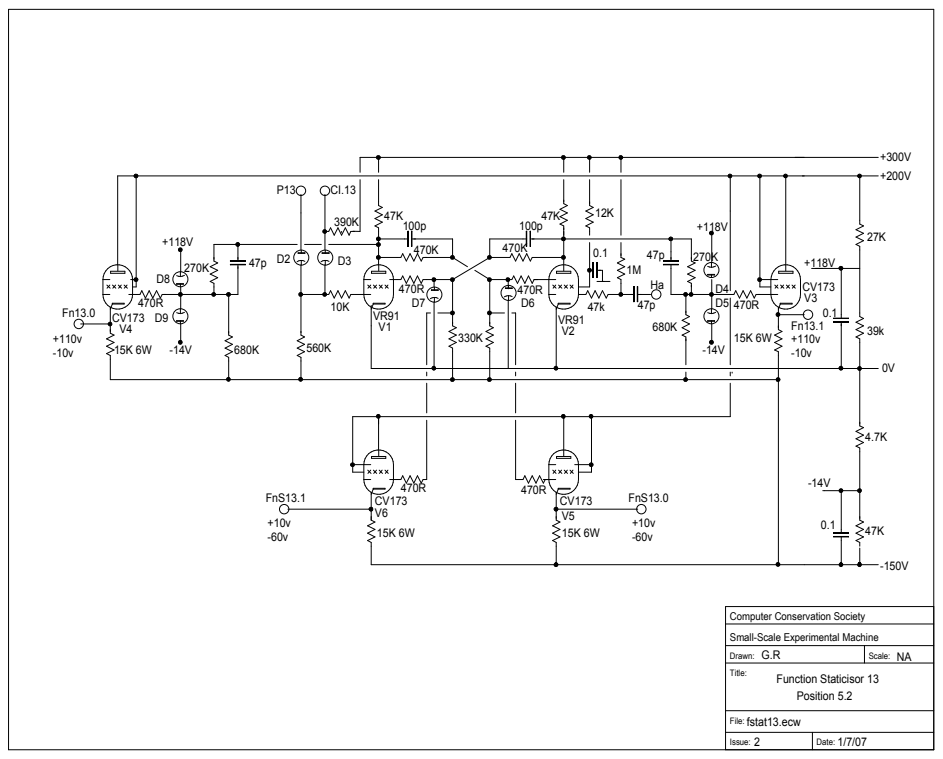
[picture p44: page 1]

Small-Scale Experimental Machine
