flypie/SSEM-Baby/Docs/fstat14.pdf

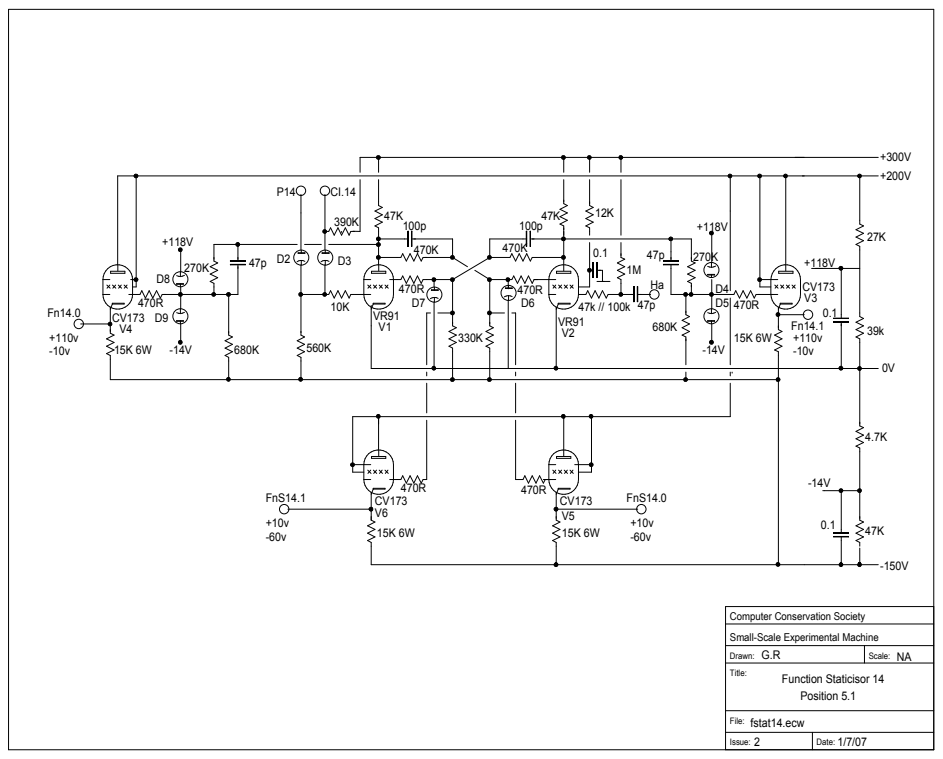
[picture p45: page 1]

Small-Scale Experimental Machine
