flypie/SSEM-Baby/Docs/fstat15.pdf

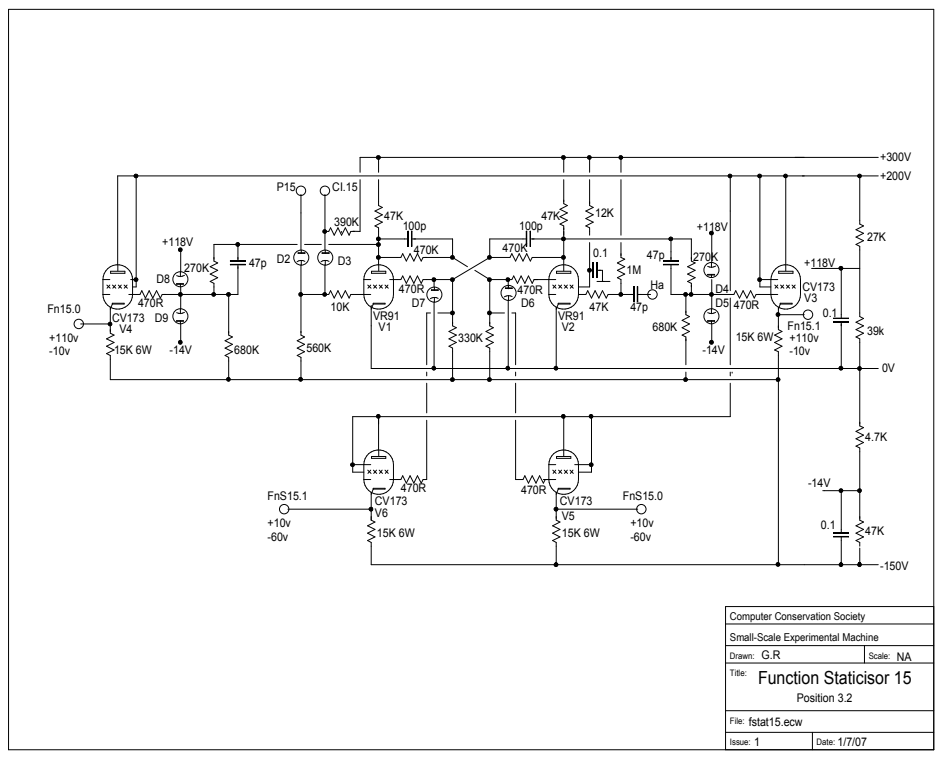
[picture p46: page 1]

Small-Scale Experimental Machine
Function Staticisor 15
