flypie/SSEM-Baby/Docs/igysh3.pdf

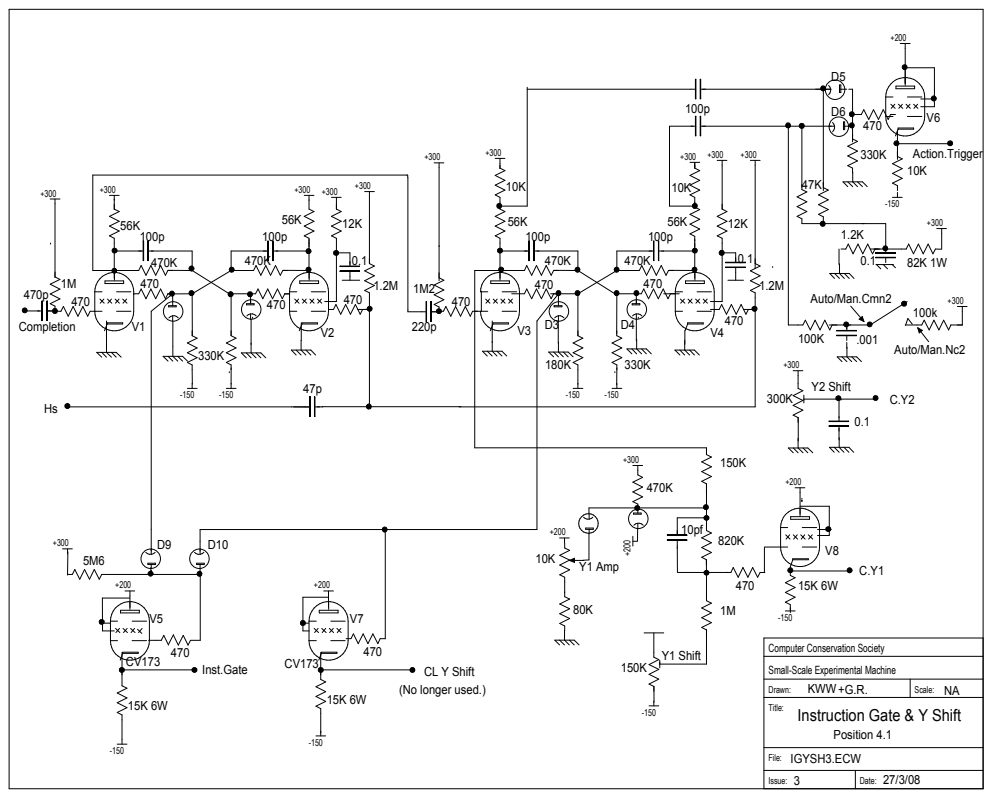
[picture p47: page 1]
Drawn:; Scale:; Title:; File:; Issue:; Date:; KWW; Completion; Y1 Shift; Y2 Shift; Inst.Gate; Action.Trigger; Auto/Man.Cmn2; Auto/Man.Nc2; IGYSH3.ECW; Instruction Gate & Y Shift; Position 4.1; Y1 Amp

Computer Conservation Society

CL Y Shift
(No longer used.)

Small-Scale Experimental Machine
