flypie/SSEM-Baby/Docs/psepctl.pdf

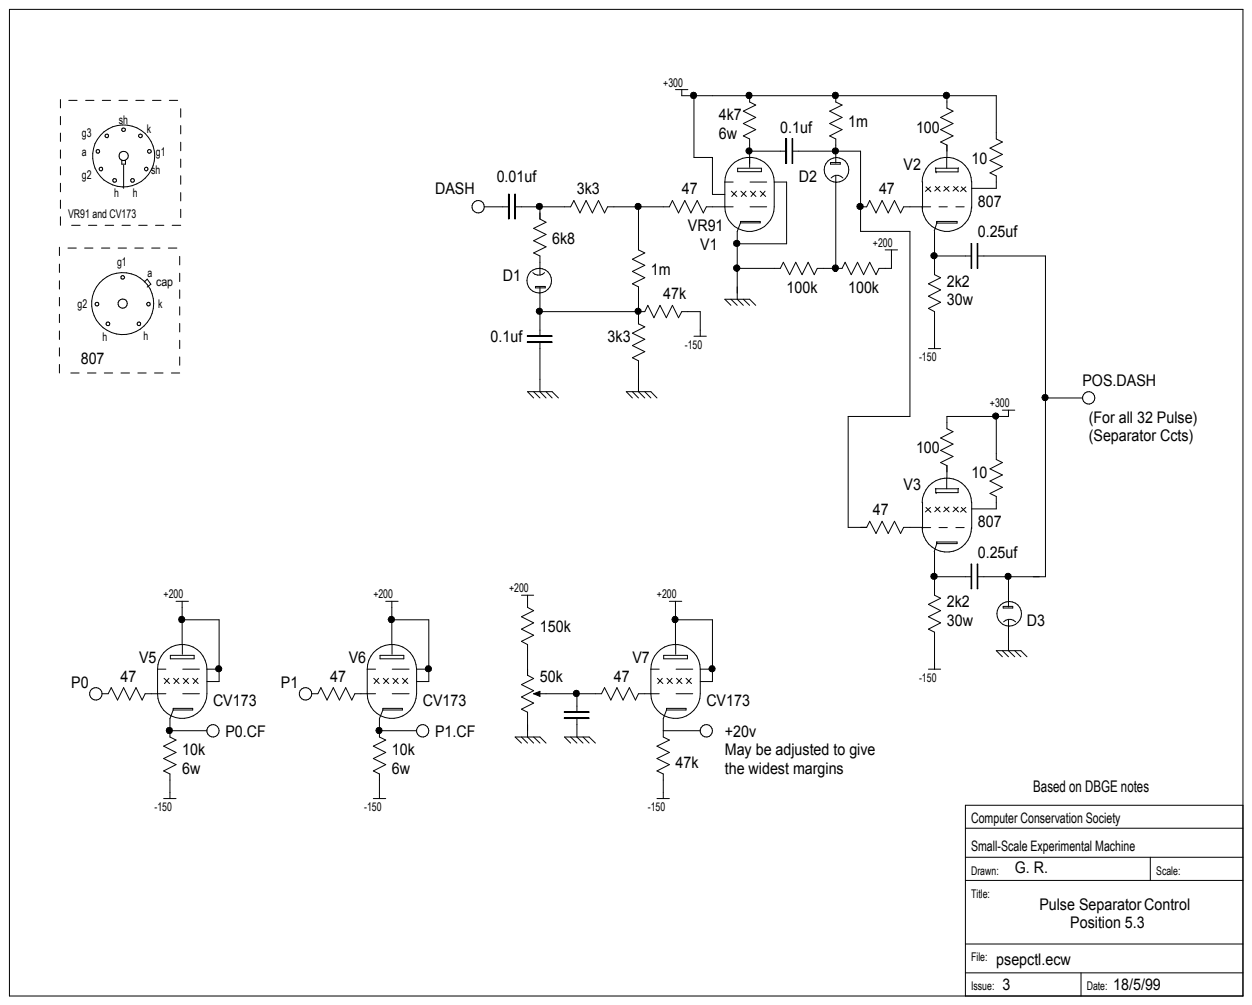
[picture p48: page 1]
Drawn:; Scale:; Title:; File:; Issue:; Date:; psepctl.ecw; DASH; POS.DASH; VR91 and CV173; cap

(For all 32 Pulse)
(Separator Ccts)

May be adjusted to give
the widest margins

Based on DBGE notes

Computer Conservation Society

Small-Scale Experimental Machine

Pulse Separator Control
Position 5.3
