flypie/SSEM-Baby/Docs/yamp&hvr.pdf

Y1 | Y2

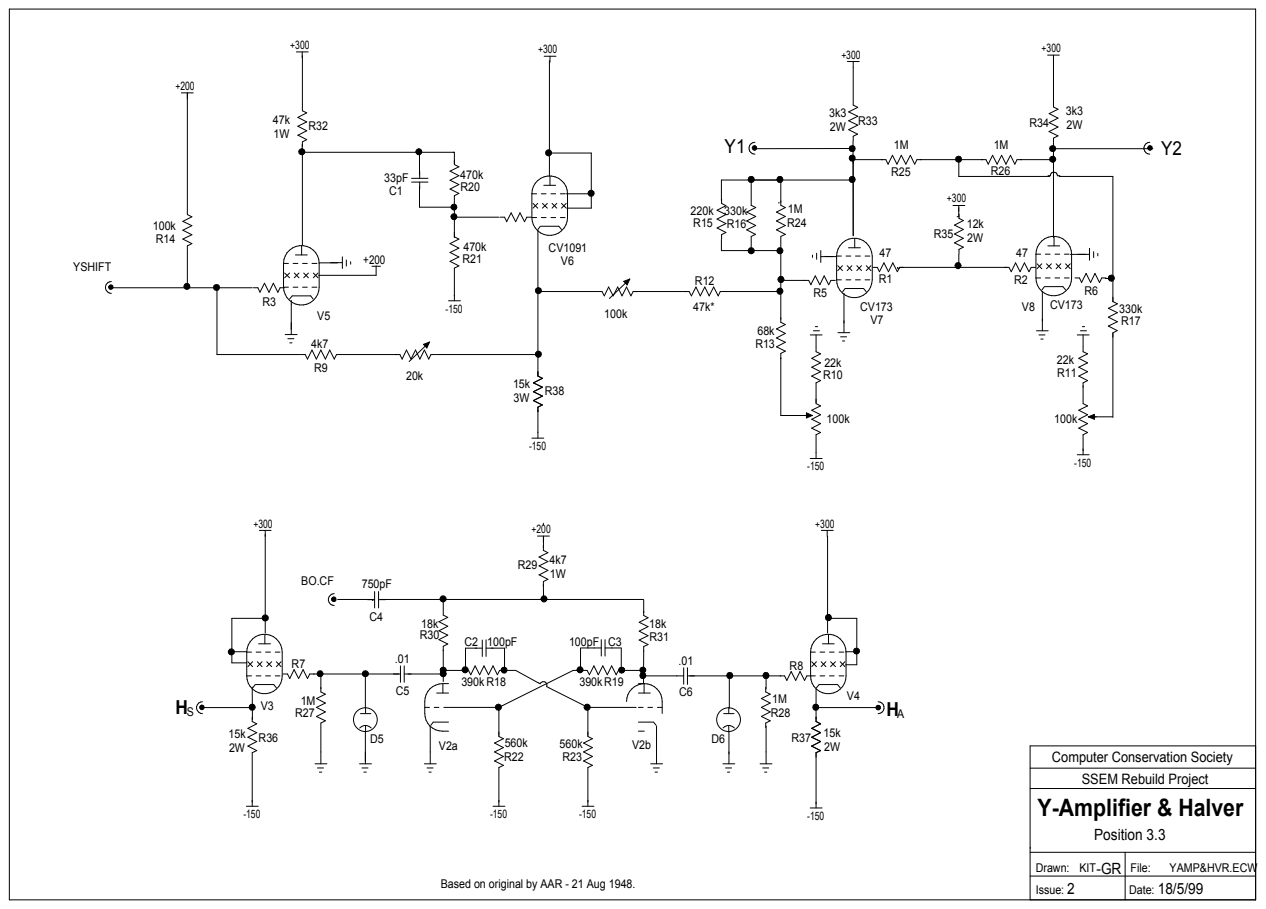
[picture p49: page 1]

Drawn: KIT -GR | File: YAMP&HVR.ECW
Issue: 2 | Date: 18/5/99

Based on original by AAR - 21 Aug 1948.
